kholia/HF-PA-v3/[Final Sim] Screenshot_2021-08-01_14-00-23.png

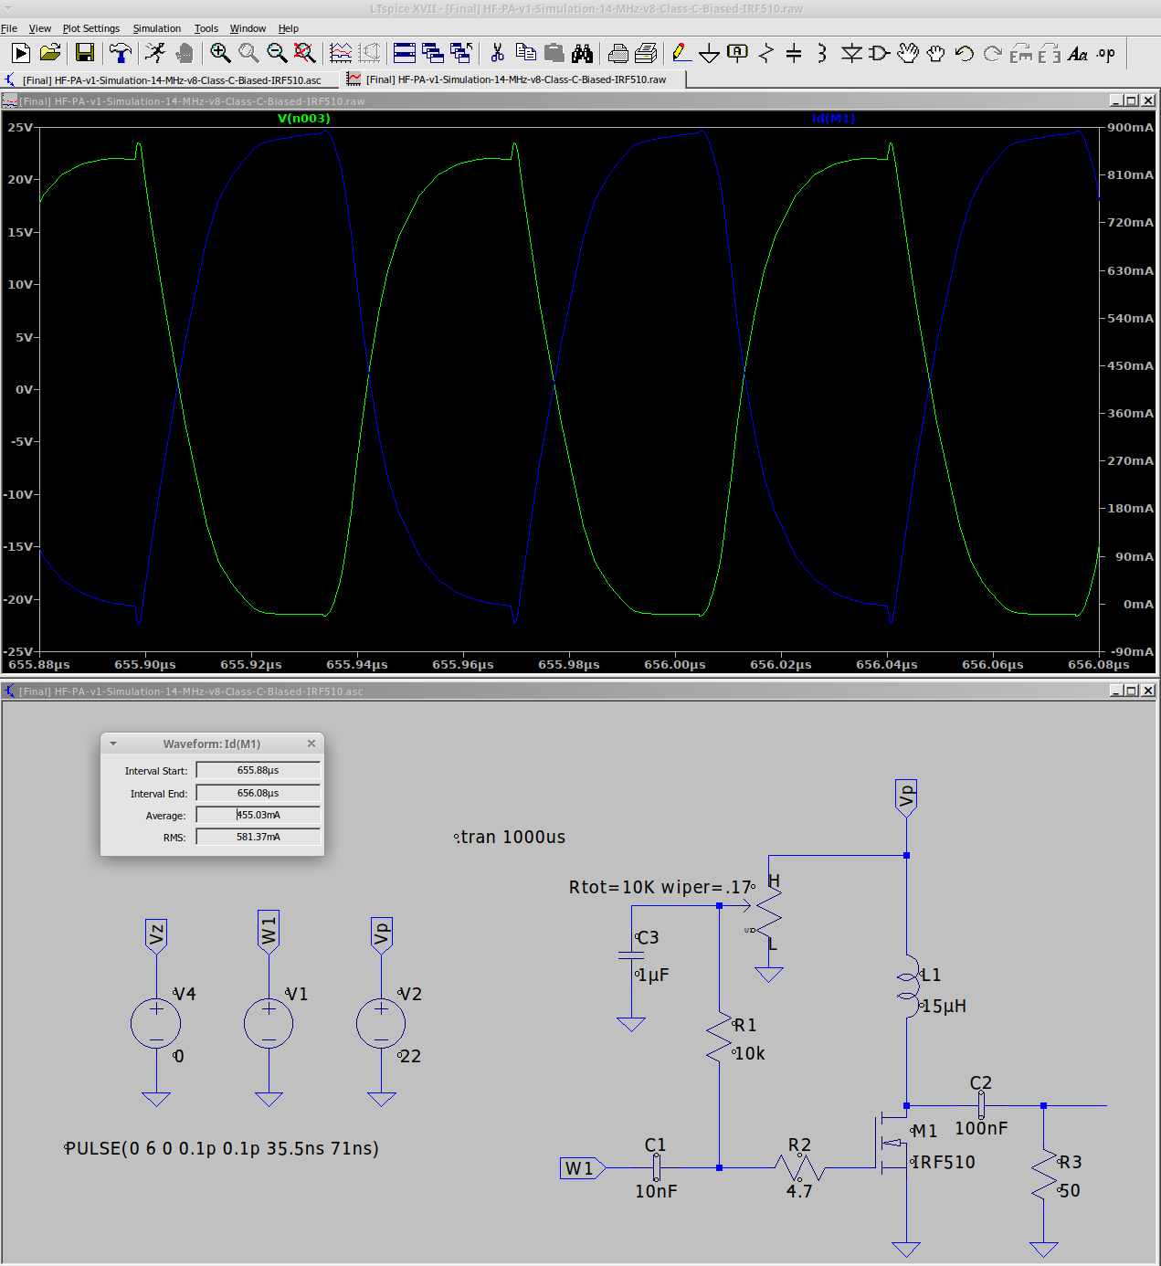
[Final Sim] Screenshot_2021-08-01_14-00-23.png
