kholia/HF-PA-v3/Genuine-Vishay-IRF510/Fun game - Which one is real? [miscdotgeek.com].jpg

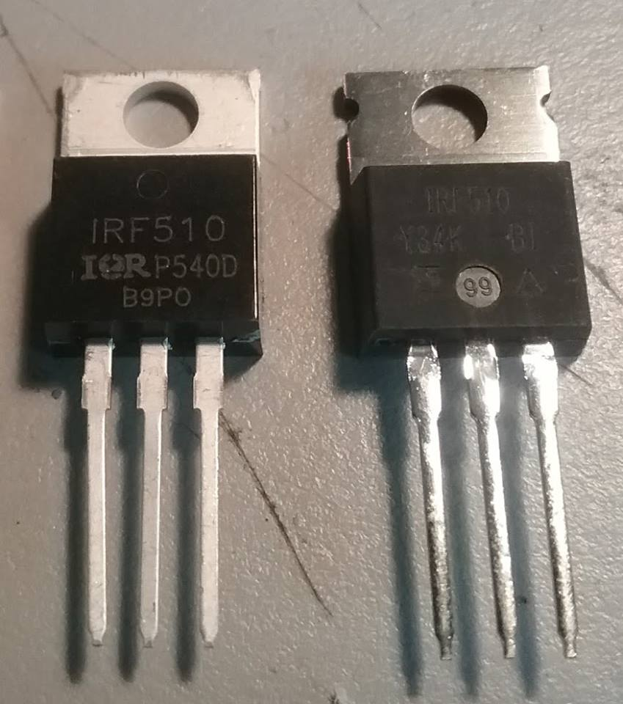
Genuine-Vishay-IRF510/Fun game - Which one is real? [miscdotgeek.com].jpg
