kholia/HF-PA-v3/Genuine-Vishay-IRF510/IRF510 MOSFET N-Channel Power MOSFETs-550x550.jpg

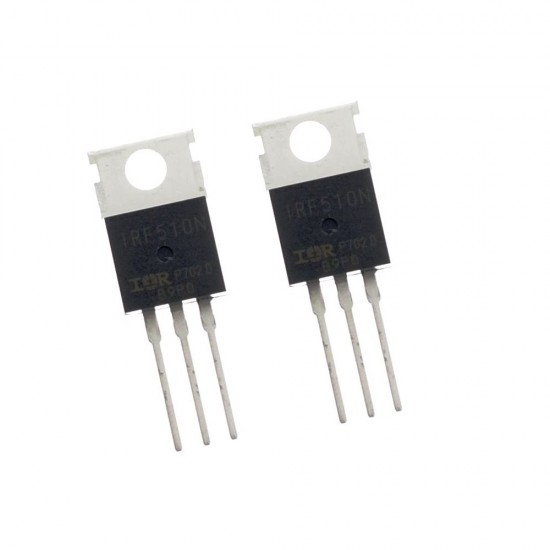
Genuine-Vishay-IRF510/IRF510 MOSFET N-Channel Power MOSFETs-550x550.jpg
