kholia/HF-PA-v3/HF-PA-Simulations/Biasing Not Helping  - Screenshot_2021-07-29_09-07-39.png

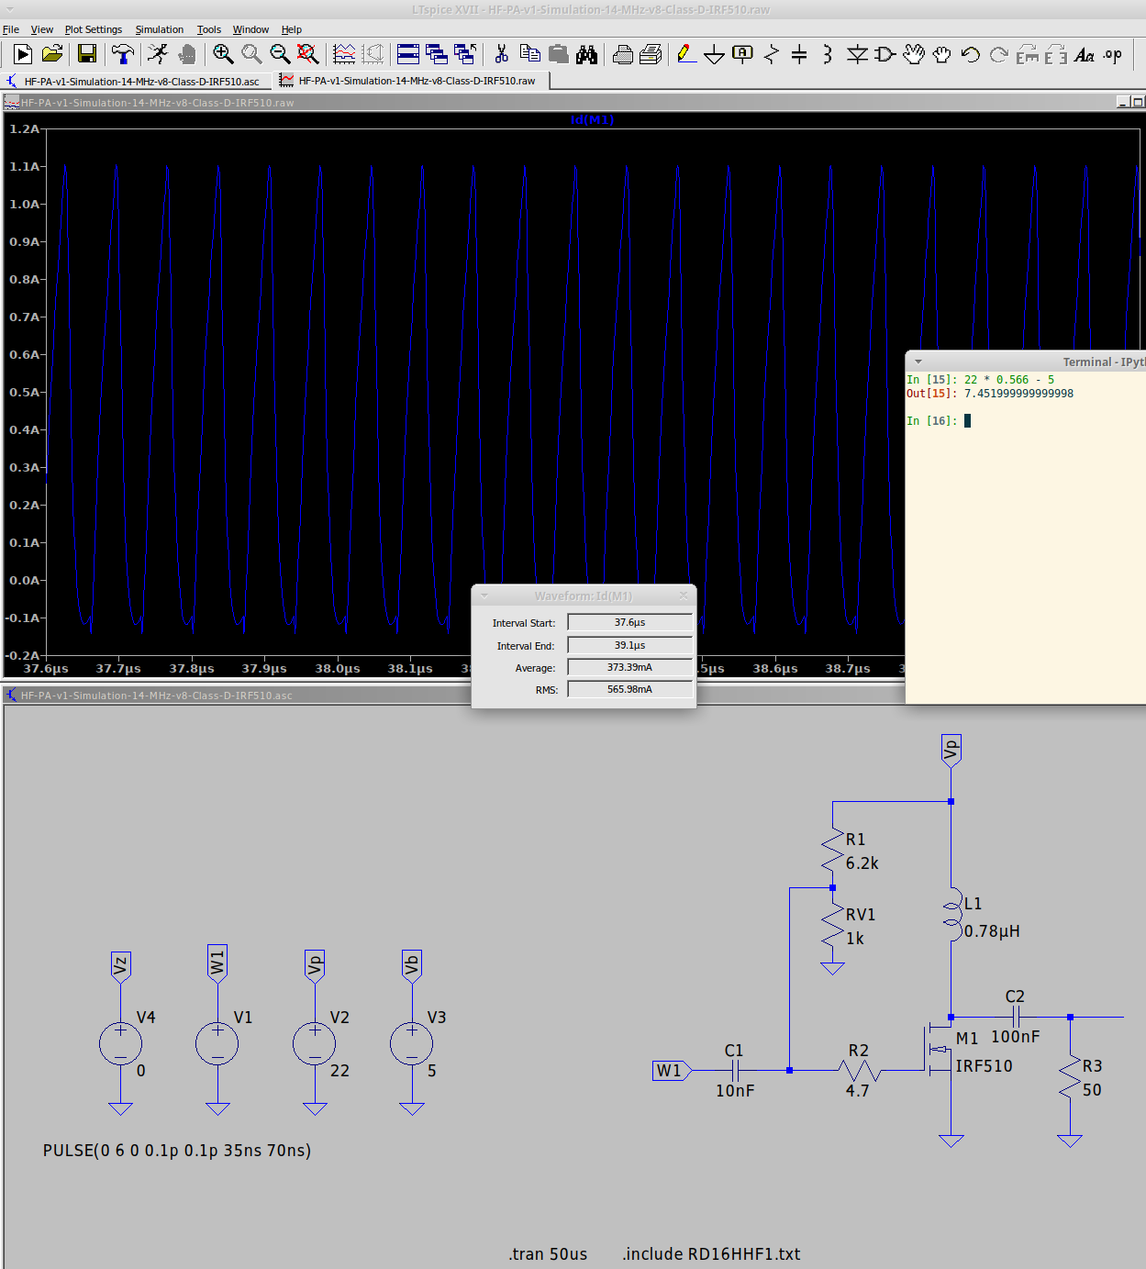
HF-PA-Simulations/Biasing Not Helping - Screenshot_2021-07-29_09-07-39.png
