kholia/HF-PA-v3/HF-PA-Simulations/Higher PA Voltage - Screenshot_2021-07-27_19-01-27.png

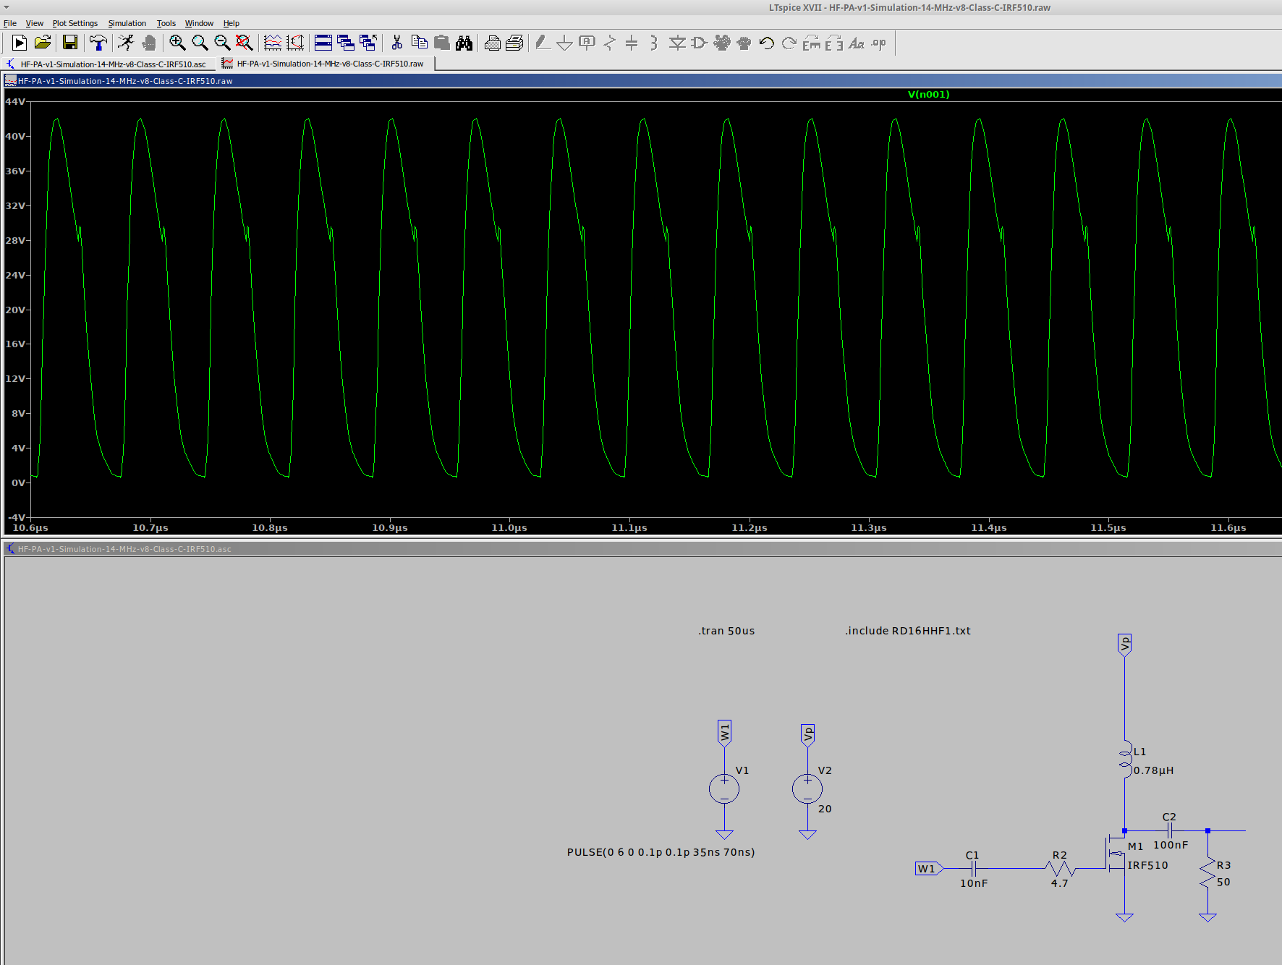
HF-PA-Simulations/Higher PA Voltage - Screenshot_2021-07-27_19-01-27.png
