kholia/HF-PA-v3/HF-PA-Simulations/Screenshot_2021-07-14_15-19-50.png

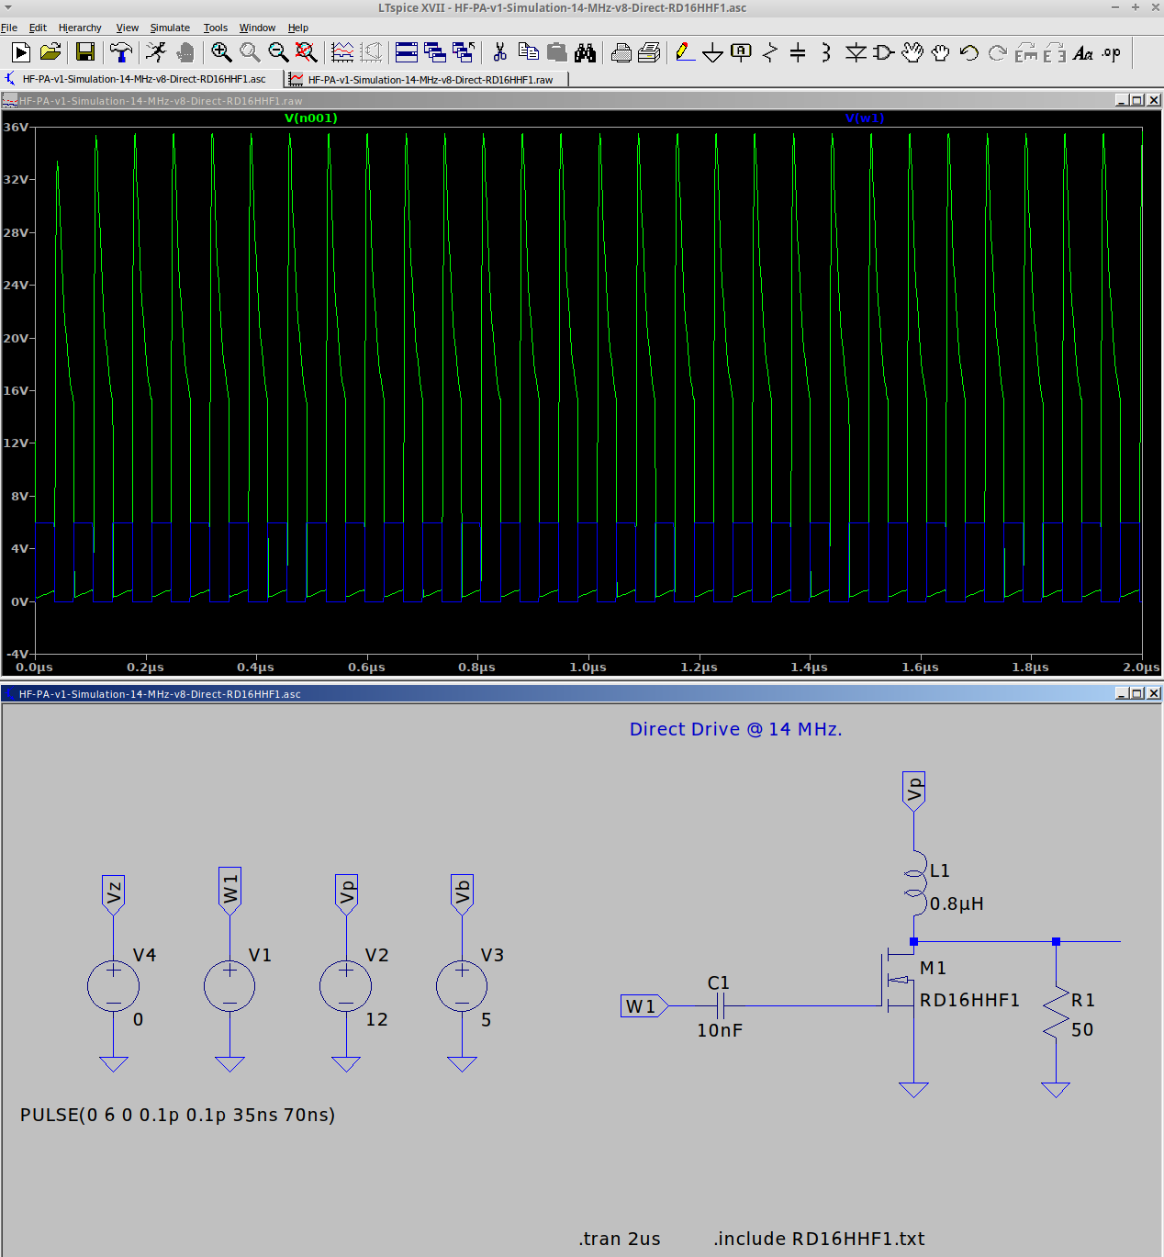
HF-PA-Simulations/Screenshot_2021-07-14_15-19-50.png
