kholia/HF-PA-v3/HF-PA-Simulations/Screenshot_2021-07-14_15-25-21.png

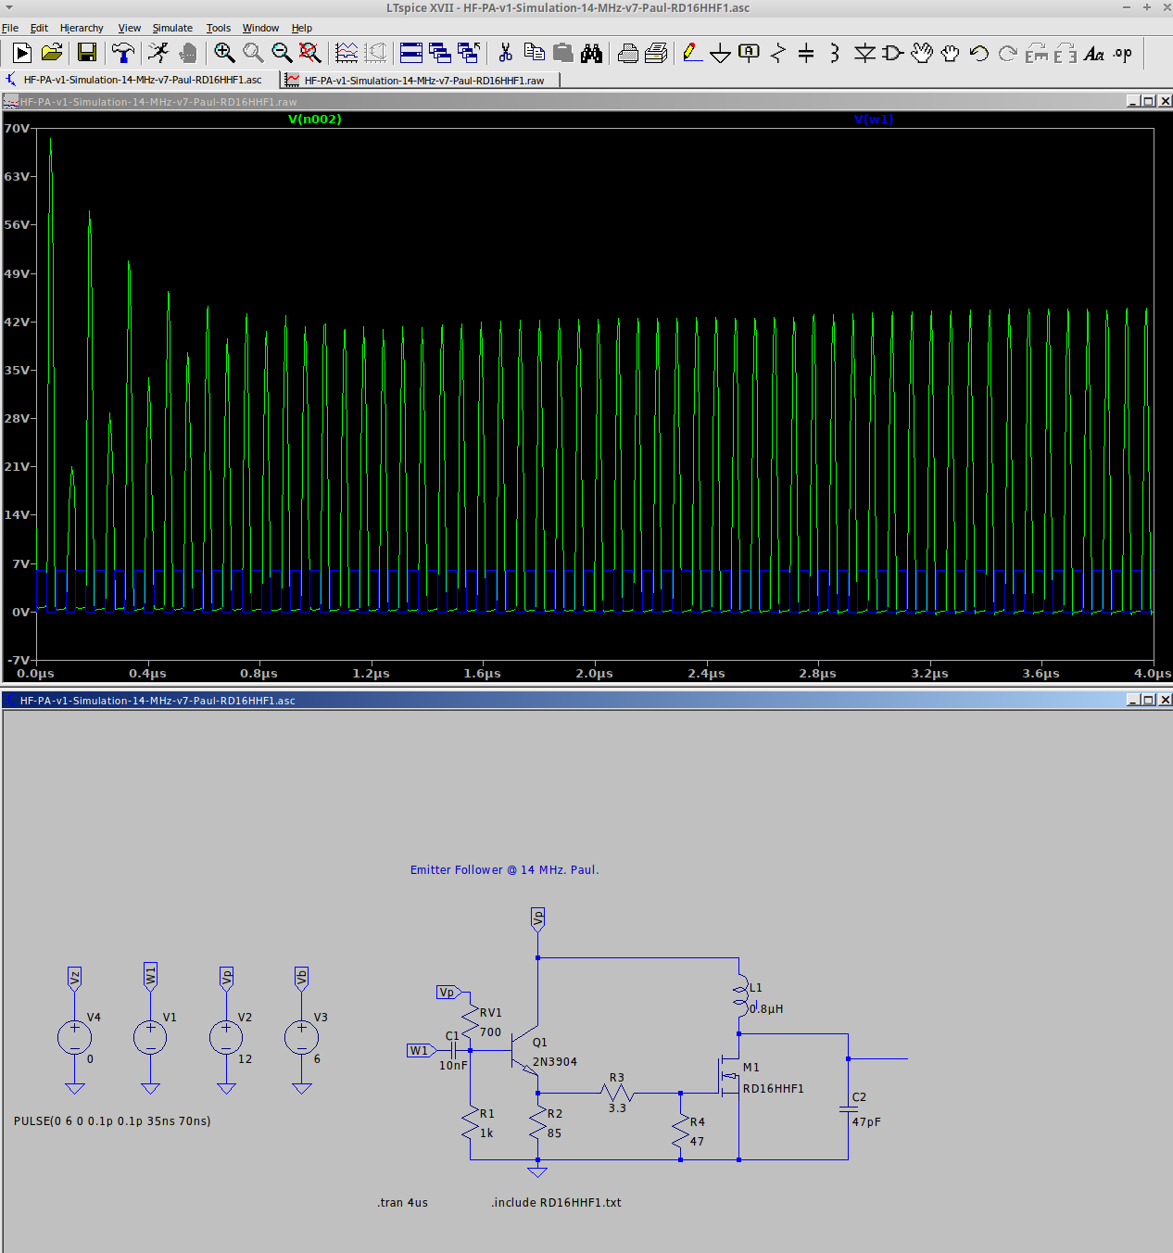
HF-PA-Simulations/Screenshot_2021-07-14_15-25-21.png
