kholia/HF-PA-v3/HF-PA-Simulations/Screenshot_2021-07-22_14-25-35.png

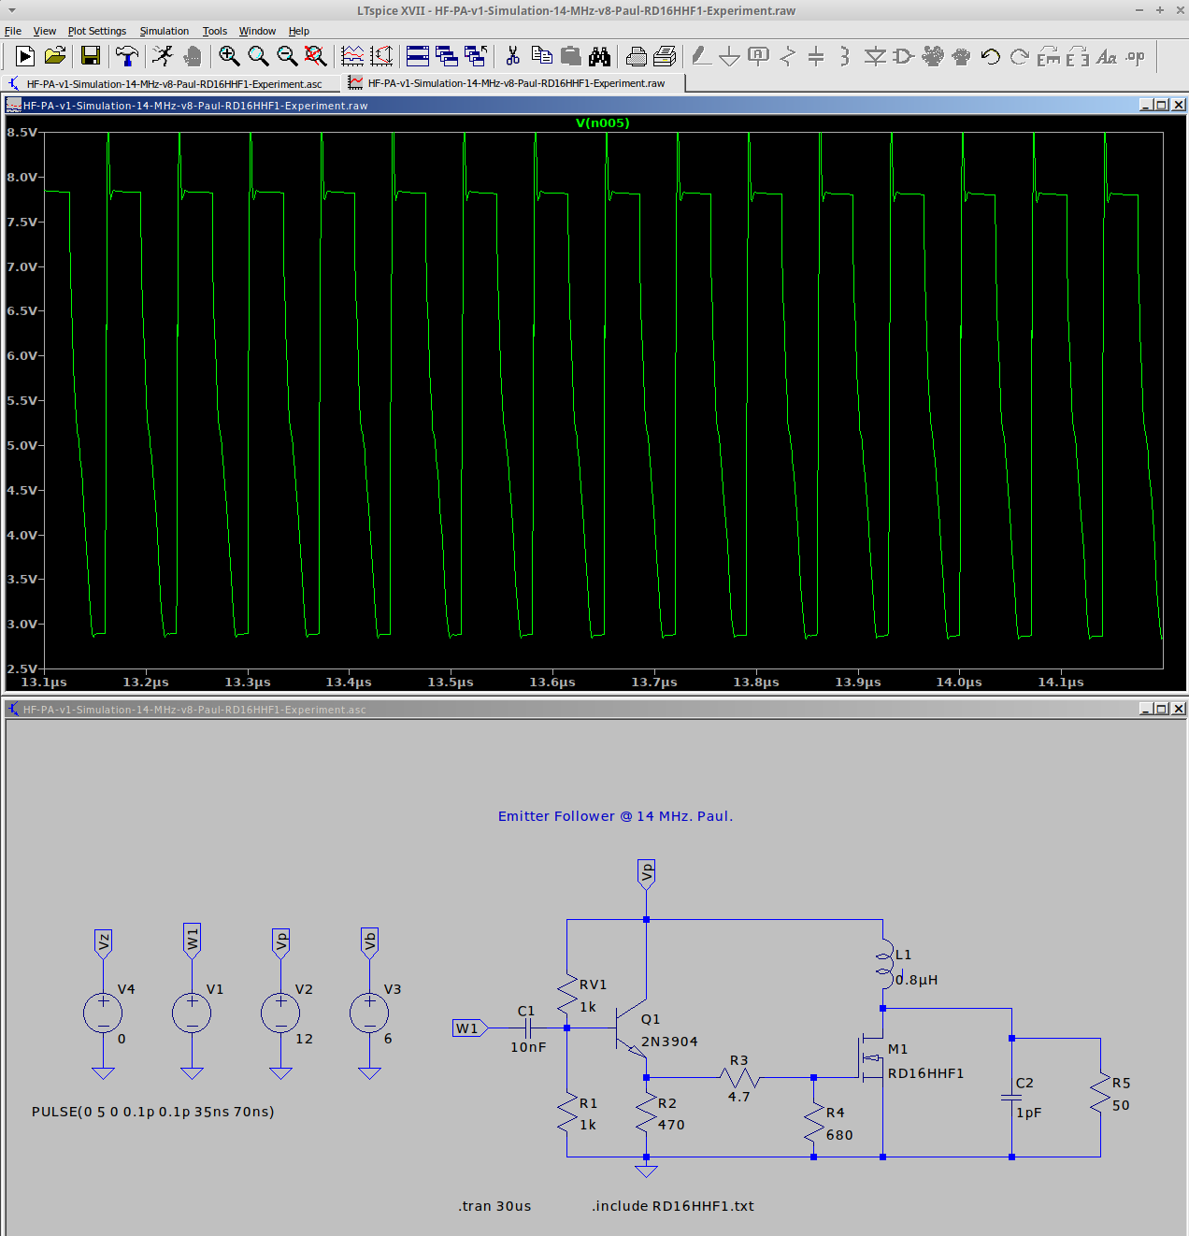
HF-PA-Simulations/Screenshot_2021-07-22_14-25-35.png
