kholia/HF-PA-v3/HF-PA-Simulations/Screenshot_2021-07-22_22-05-22.png

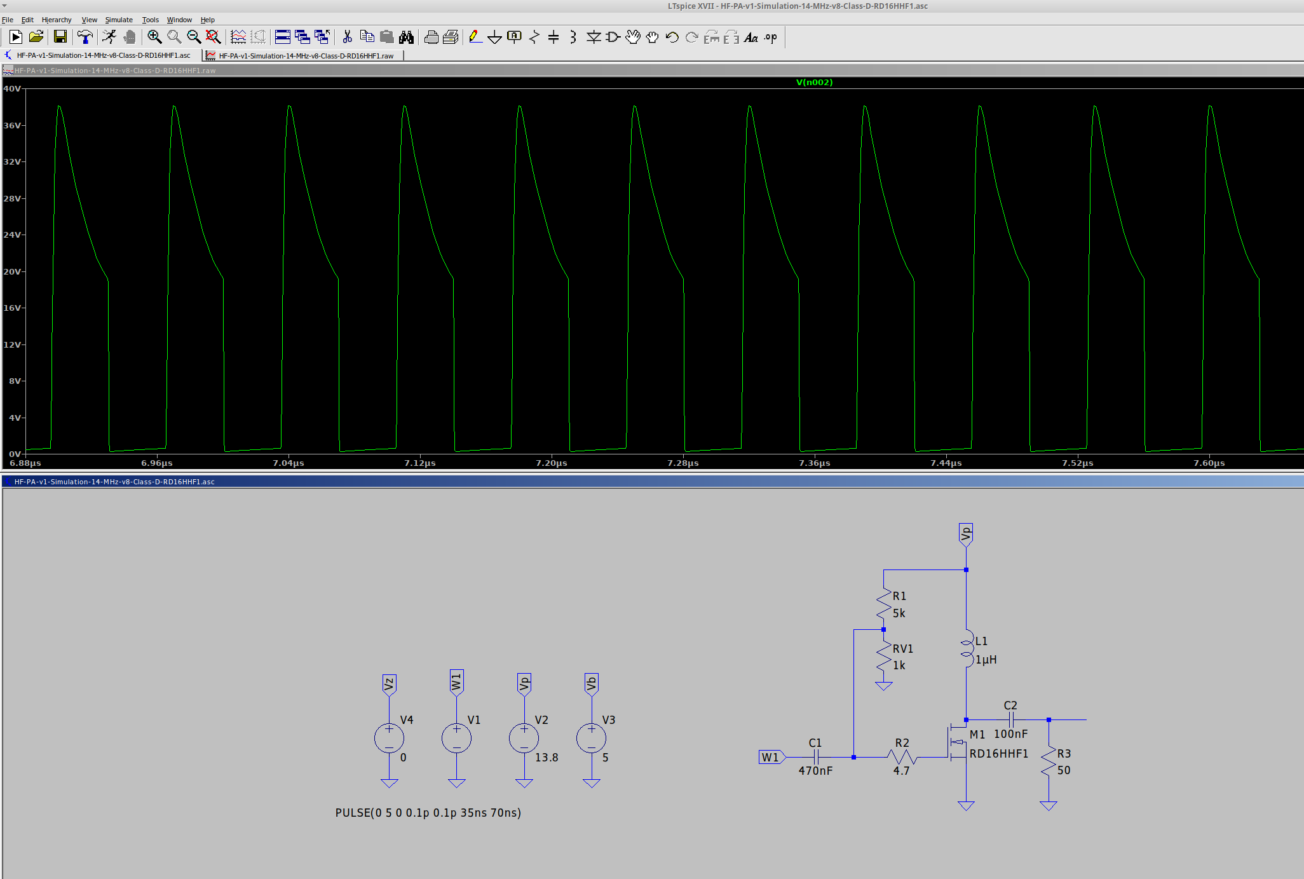
HF-PA-Simulations/Screenshot_2021-07-22_22-05-22.png
