kholia/HF-PA-v3/HF-PA-Simulations/Screenshot_2021-07-27_22-03-09.png

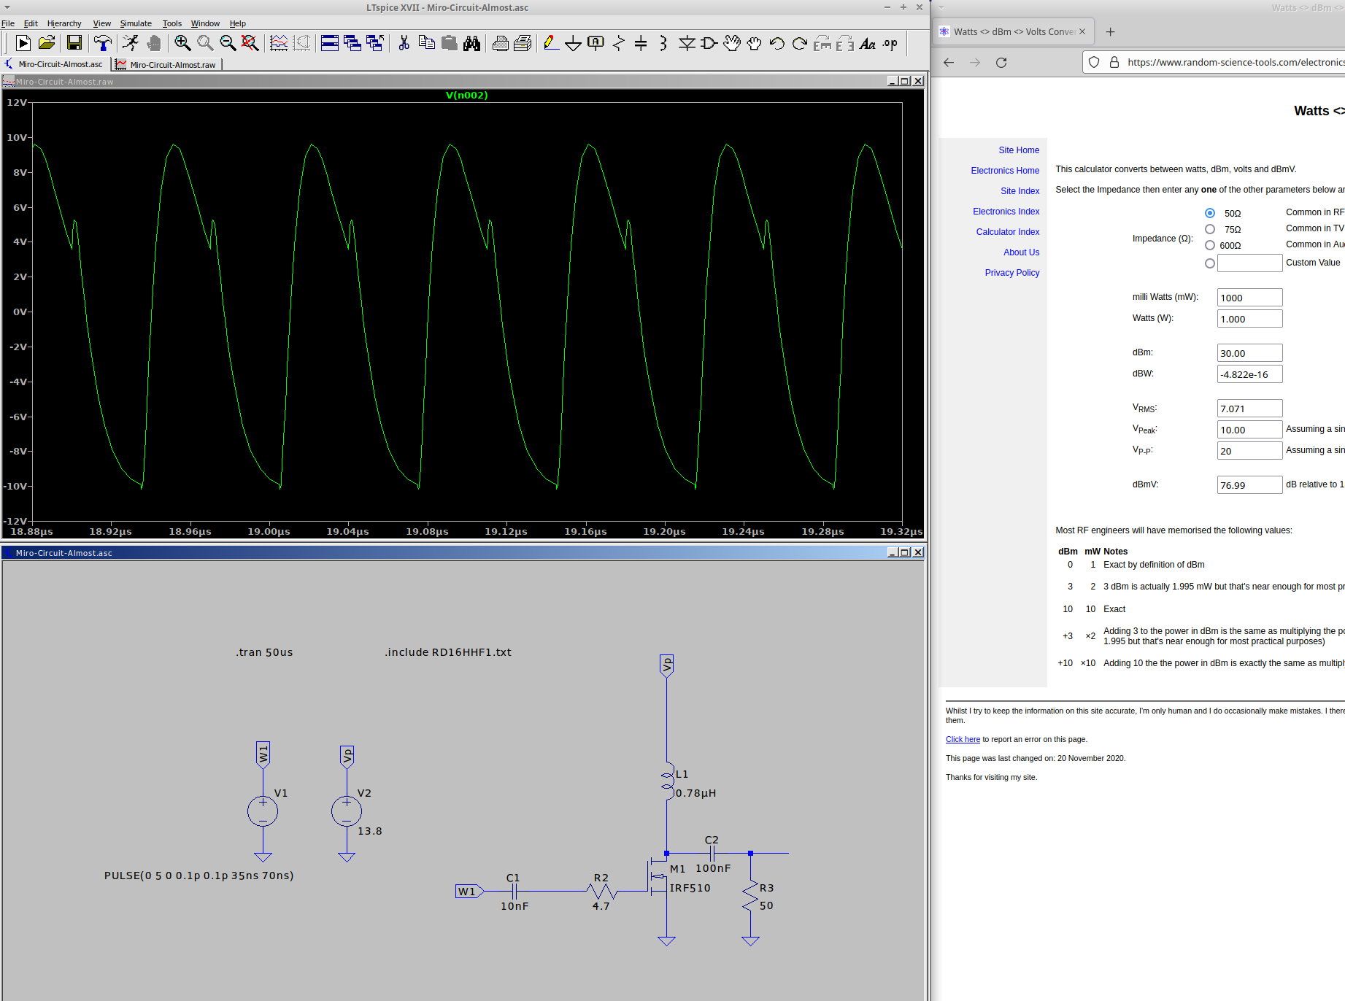
HF-PA-Simulations/Screenshot_2021-07-27_22-03-09.png
