kholia/HF-PA-v3/HF-PA-Simulations/Screenshot_2021-07-27_22-06-03.png

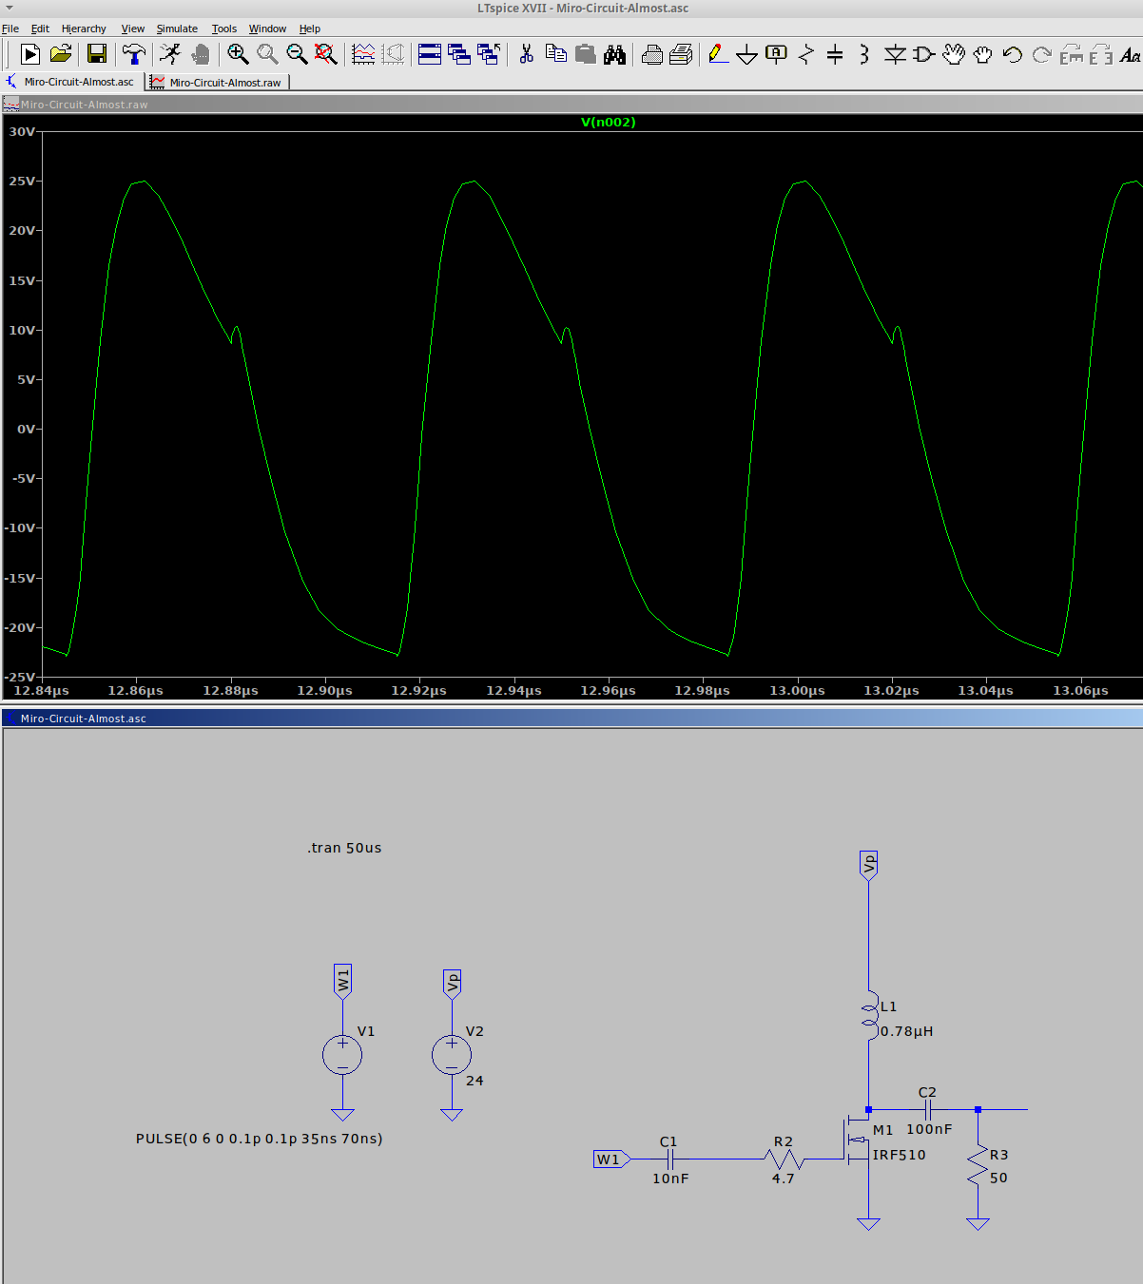
HF-PA-Simulations/Screenshot_2021-07-27_22-06-03.png
