kholia/HF-PA-v3/HF-PA-Simulations/Screenshot_2021-07-28_18-34-36.png

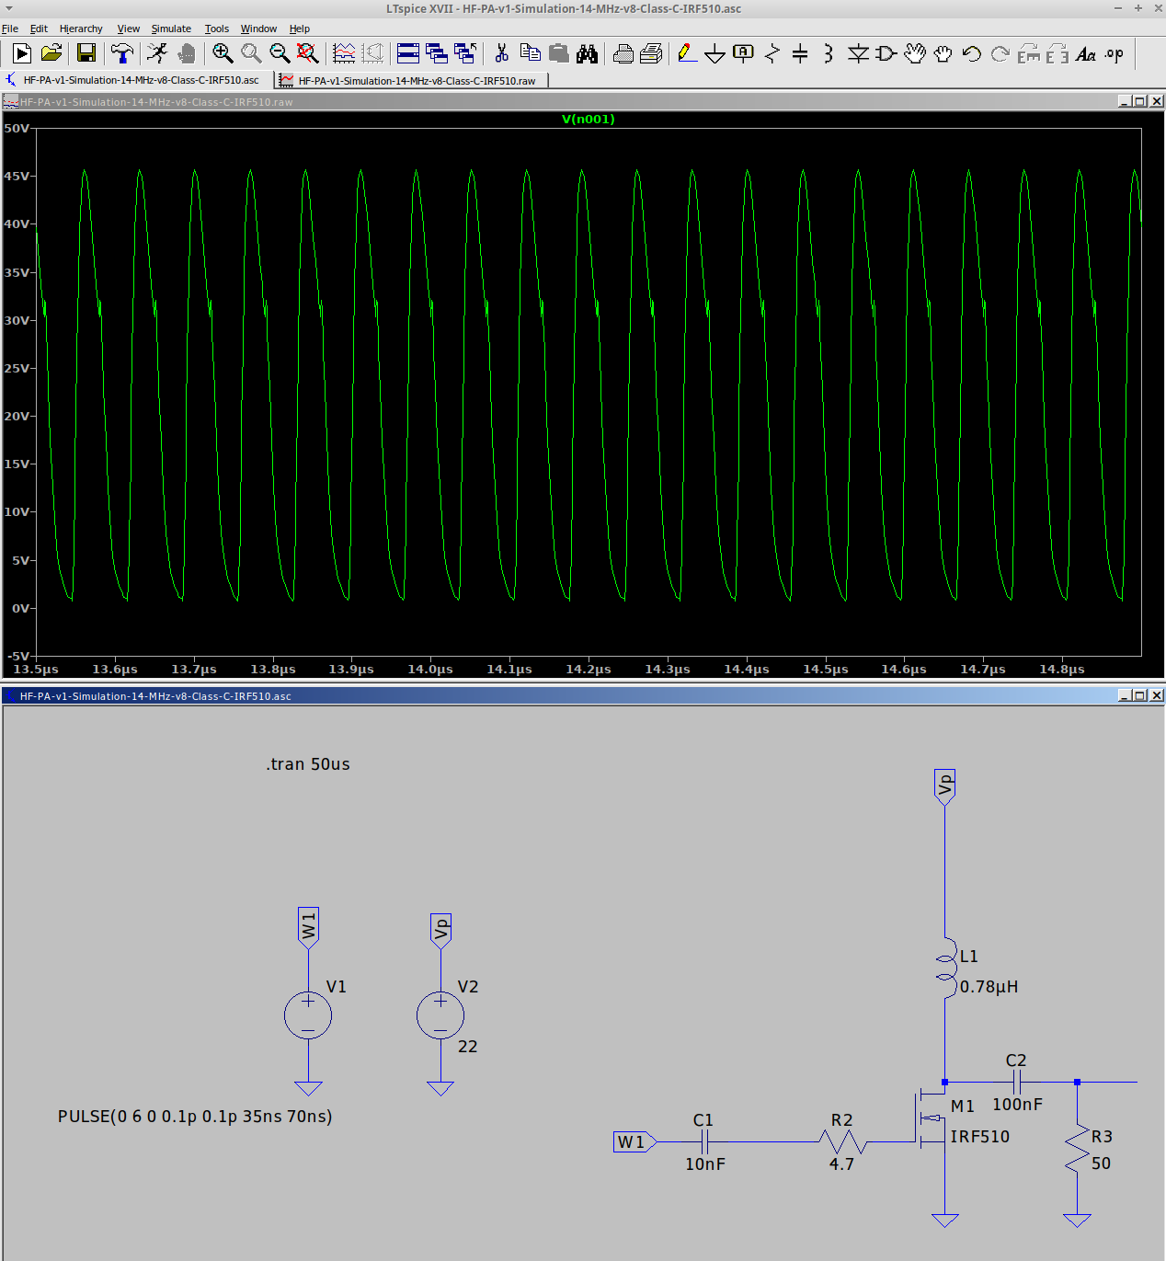
HF-PA-Simulations/Screenshot_2021-07-28_18-34-36.png
