kholia/HF-PA-v3/HF-PA-Simulations/Screenshot_2021-07-29_00-05-49.png

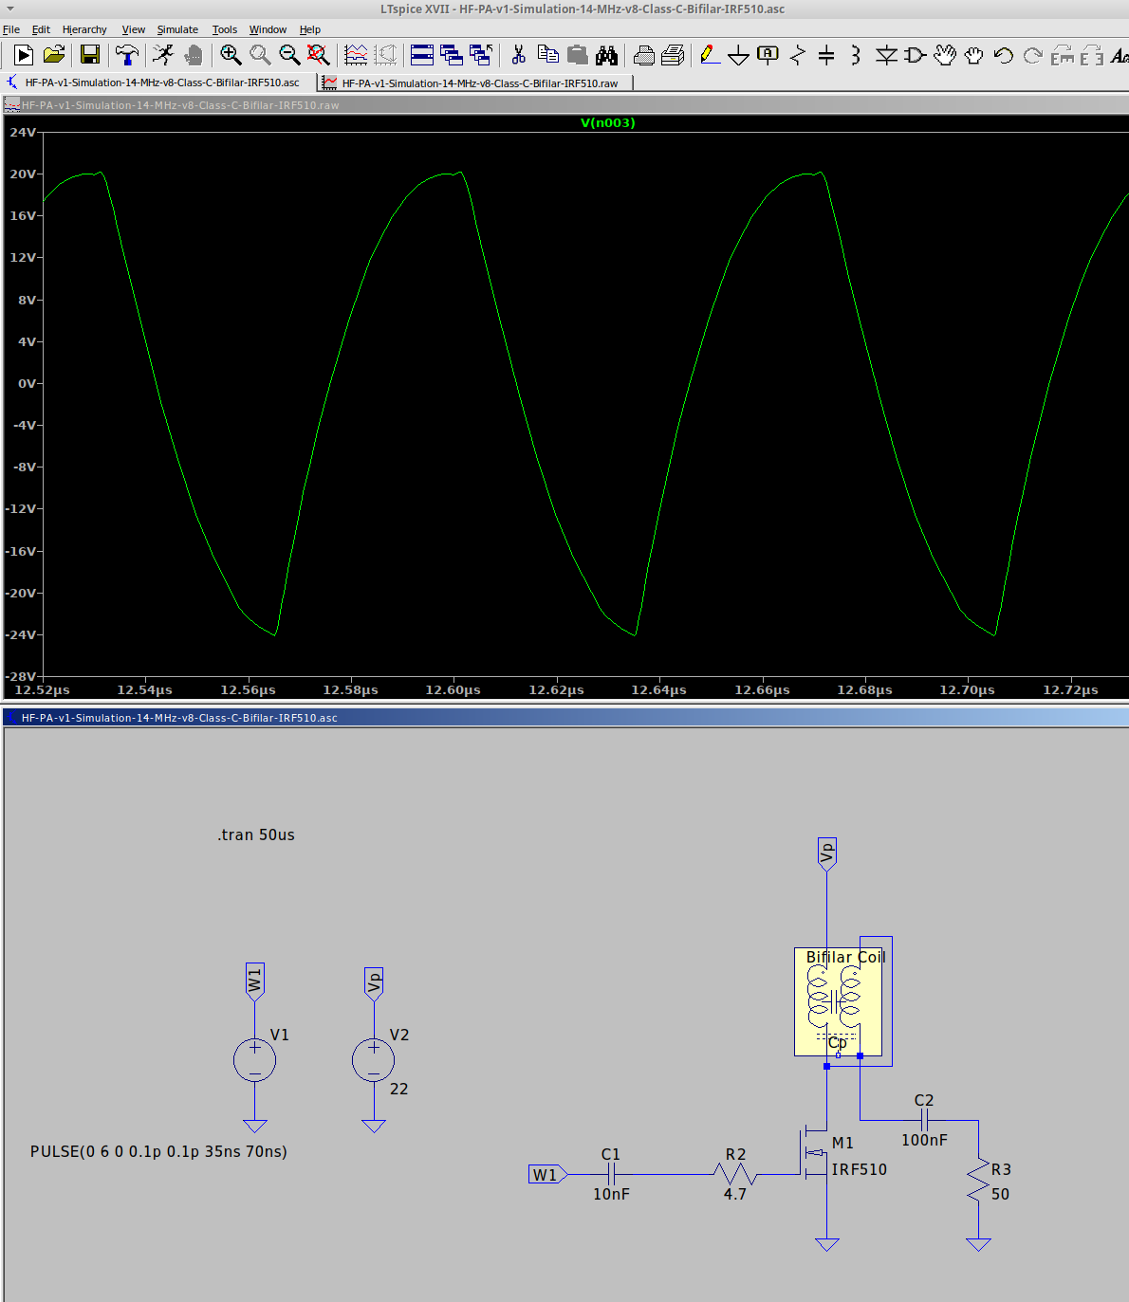
HF-PA-Simulations/Screenshot_2021-07-29_00-05-49.png
