kholia/HF-PA-v3/HF-PA-Simulations/Screenshot_2021-07-29_00-10-33.png

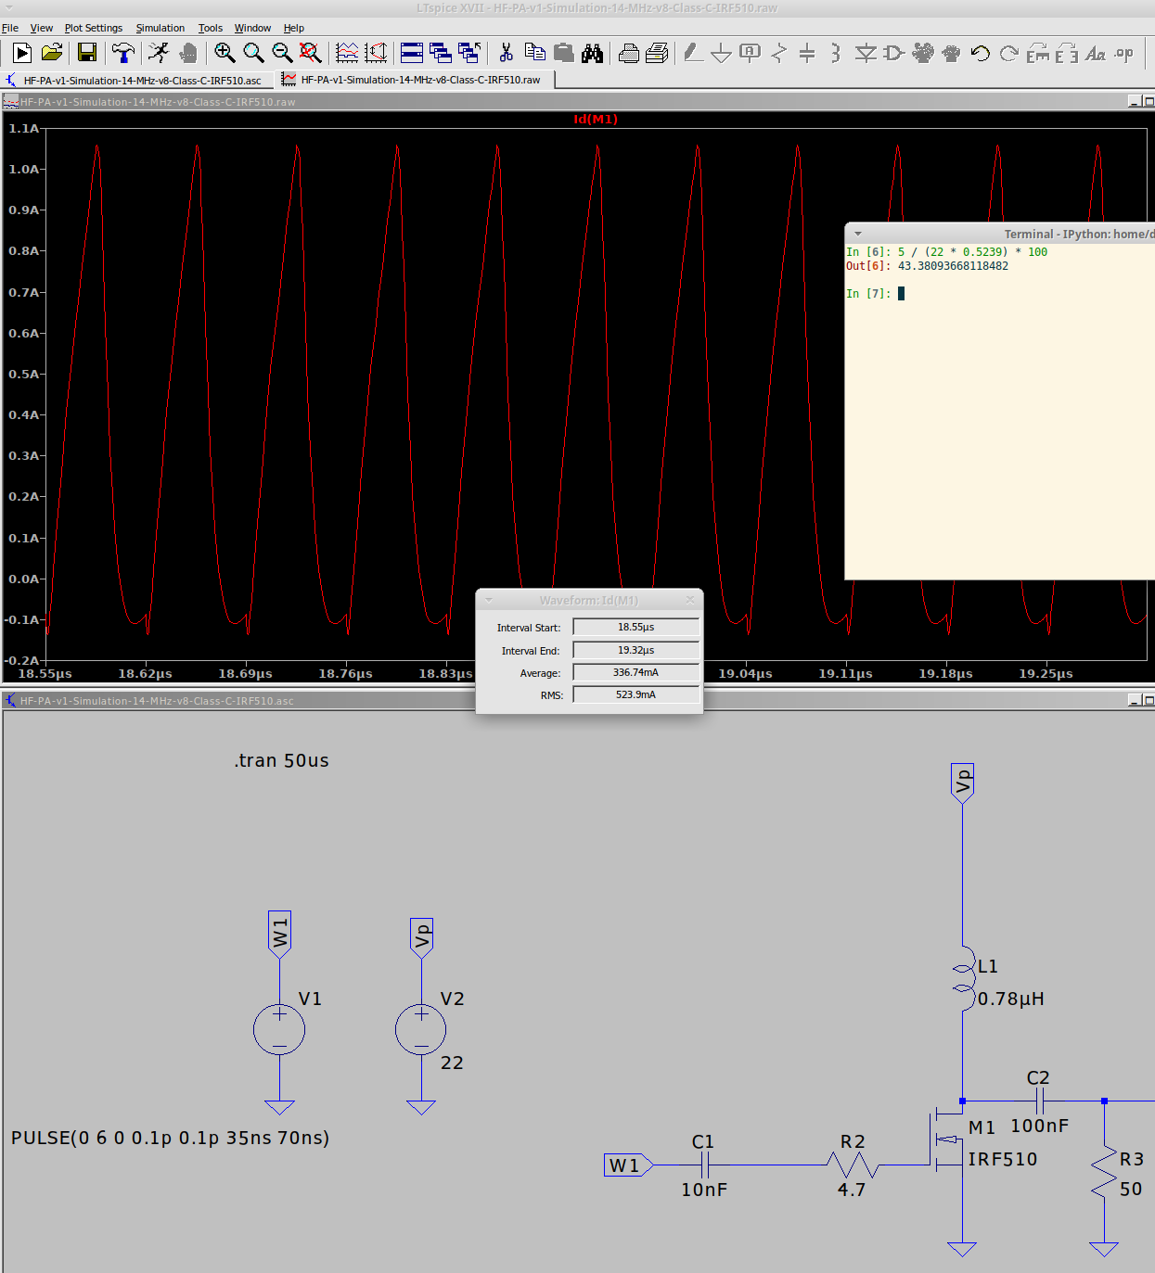
HF-PA-Simulations/Screenshot_2021-07-29_00-10-33.png
