kholia/HF-PA-v3/Info/40m-lpf-filter-as-built.png

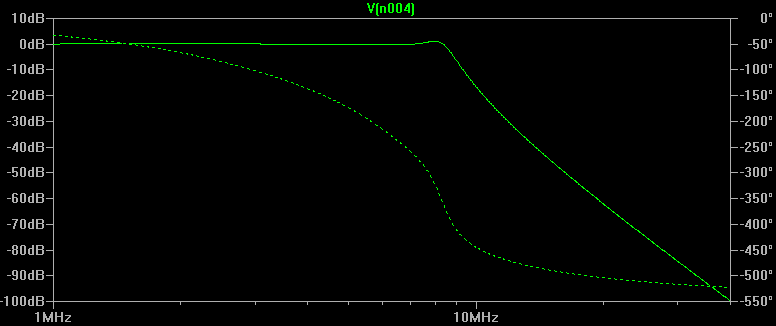
Info/40m-lpf-filter-as-built.png
