kholia/HF-PA-v3/Info/1513-2-550x550w.JPG

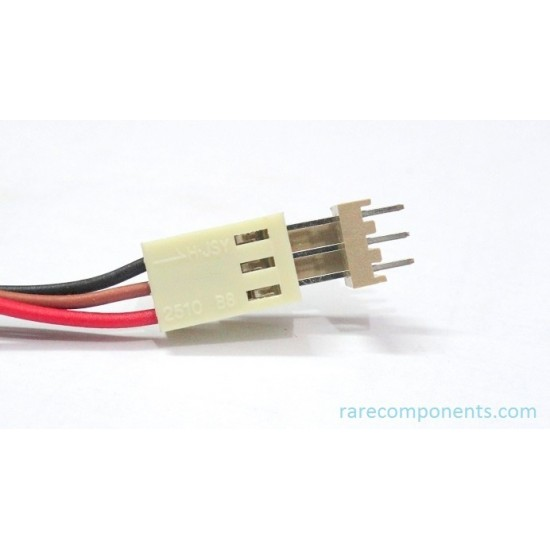
Info/1513-2-550x550w.JPG
