kholia/HF-PA-v3/Info/[Earthing Tip] - Screenshot_2021-07-30_19-18-58.png

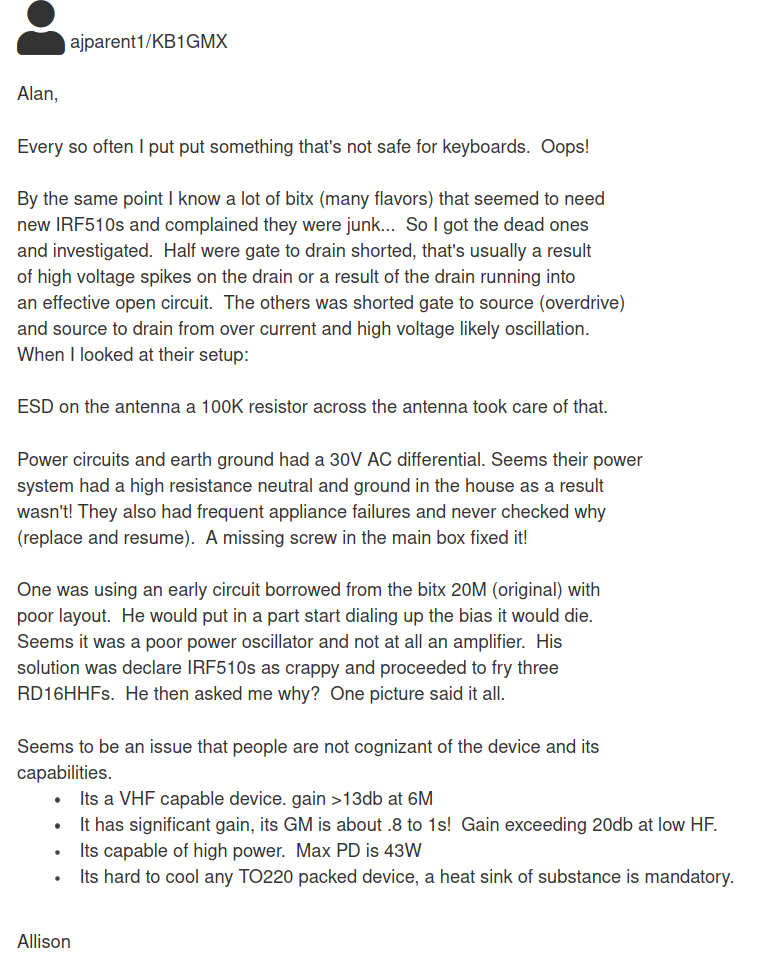
Info/[Earthing Tip] - Screenshot_2021-07-30_19-18-58.png
