kholia/HF-PA-v3/Info/fan-circuit-pulldown-640x349.png

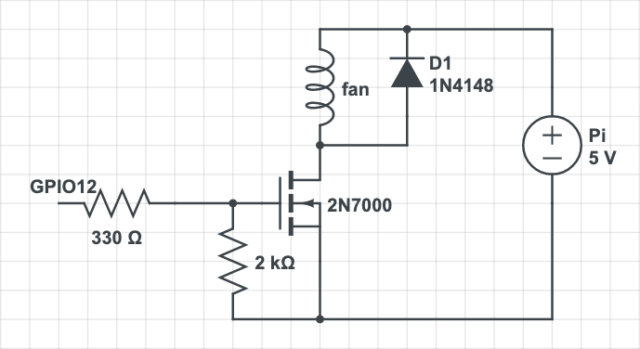
Info/fan-circuit-pulldown-640x349.png
