kholia/HF-PA-v3/Info/IRF510-mod.jpeg

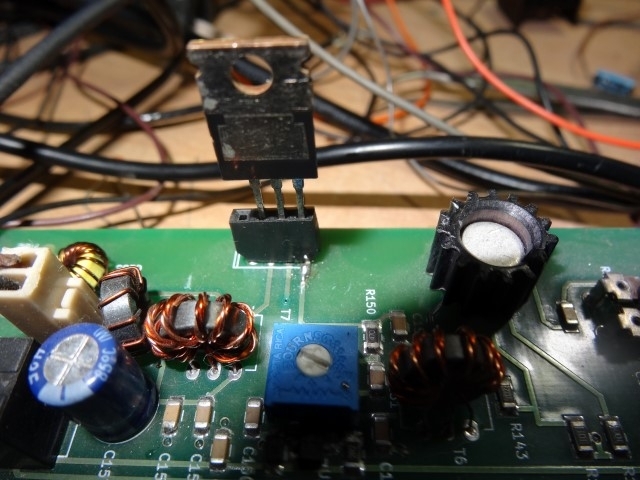
Info/IRF510-mod.jpeg
