kholia/HF-PA-v3/Info/kk9jef-lpf.jpg

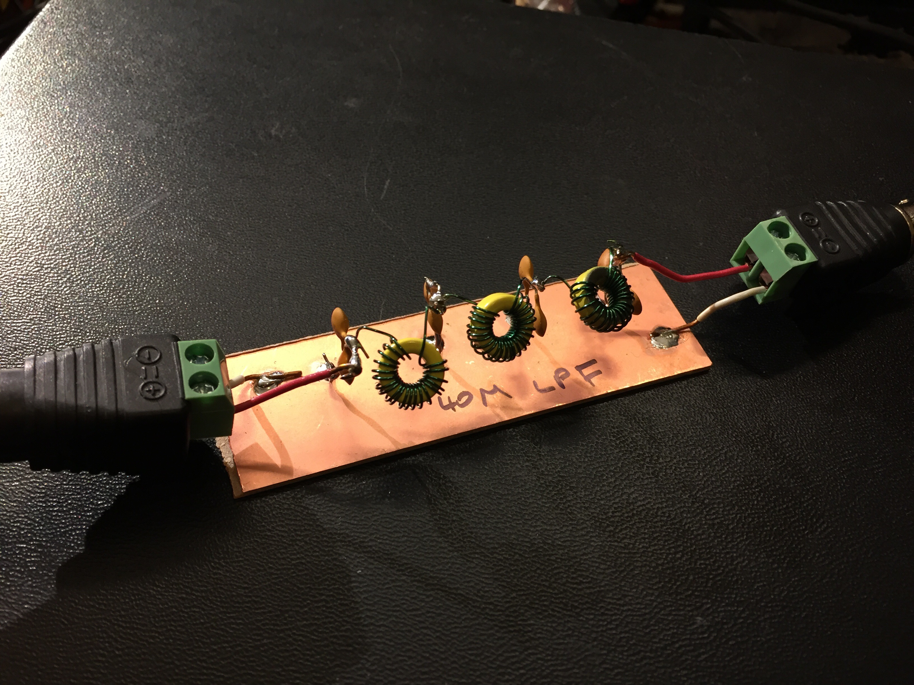
Info/kk9jef-lpf.jpg
