kholia/HF-PA-v3/Info/LPF-Details-Screenshot_2021-09-19_14-00-25.png

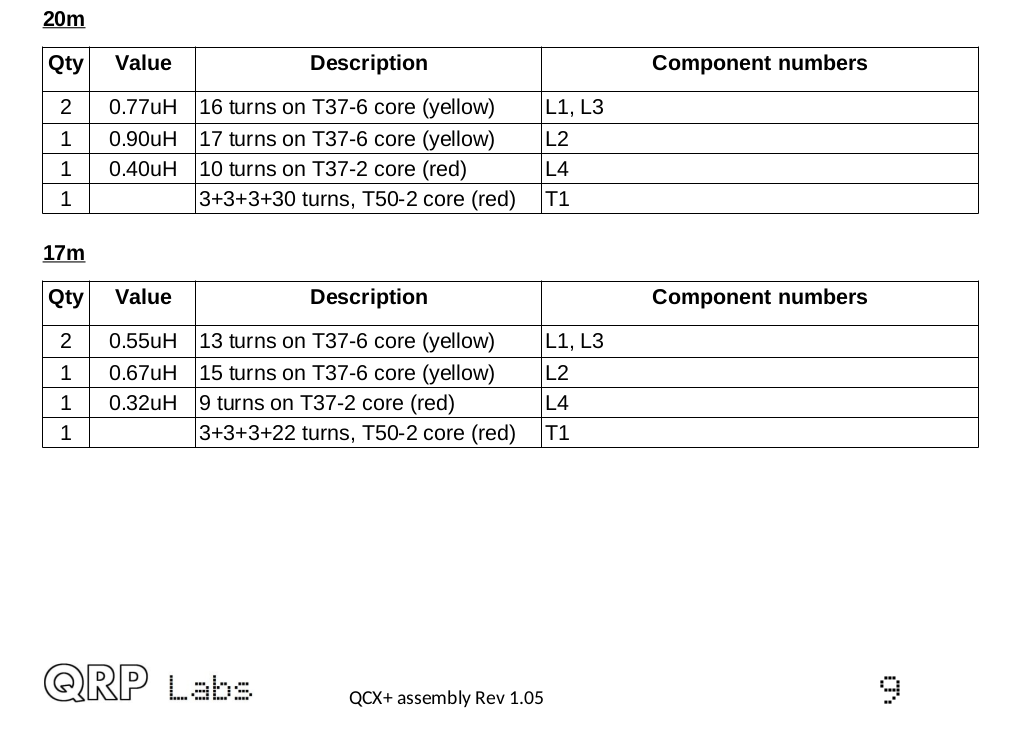
Info/LPF-Details-Screenshot_2021-09-19_14-00-25.png
