kholia/HF-PA-v3/Info/LPF-Screenshot_2021-09-19_14-16-24.png

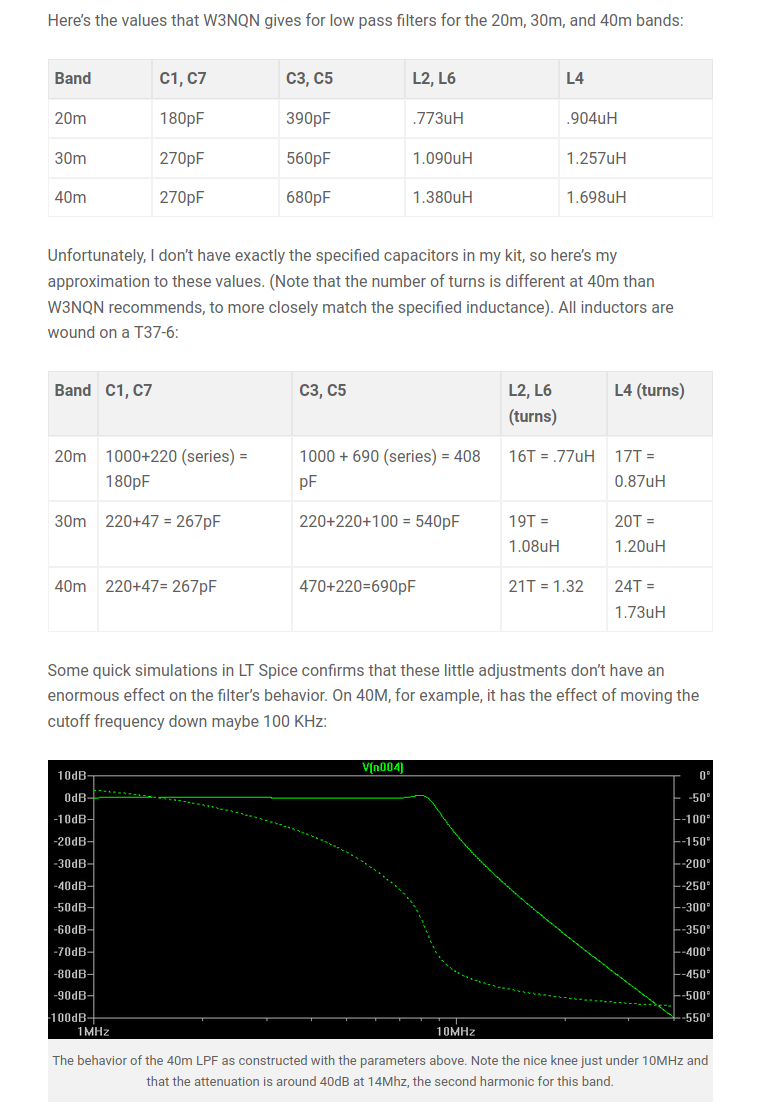
Info/LPF-Screenshot_2021-09-19_14-16-24.png
