kholia/HF-PA-v3/Info/lpf-sketch.png

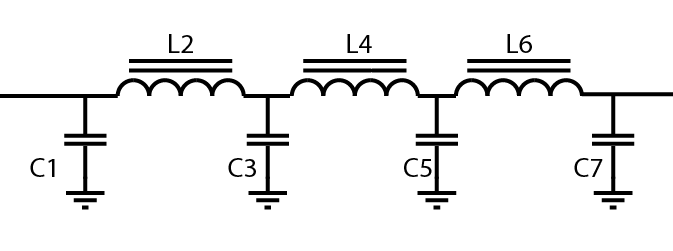
Info/lpf-sketch.png
