kholia/HF-PA-v3/Info/lulu-RF.bmp

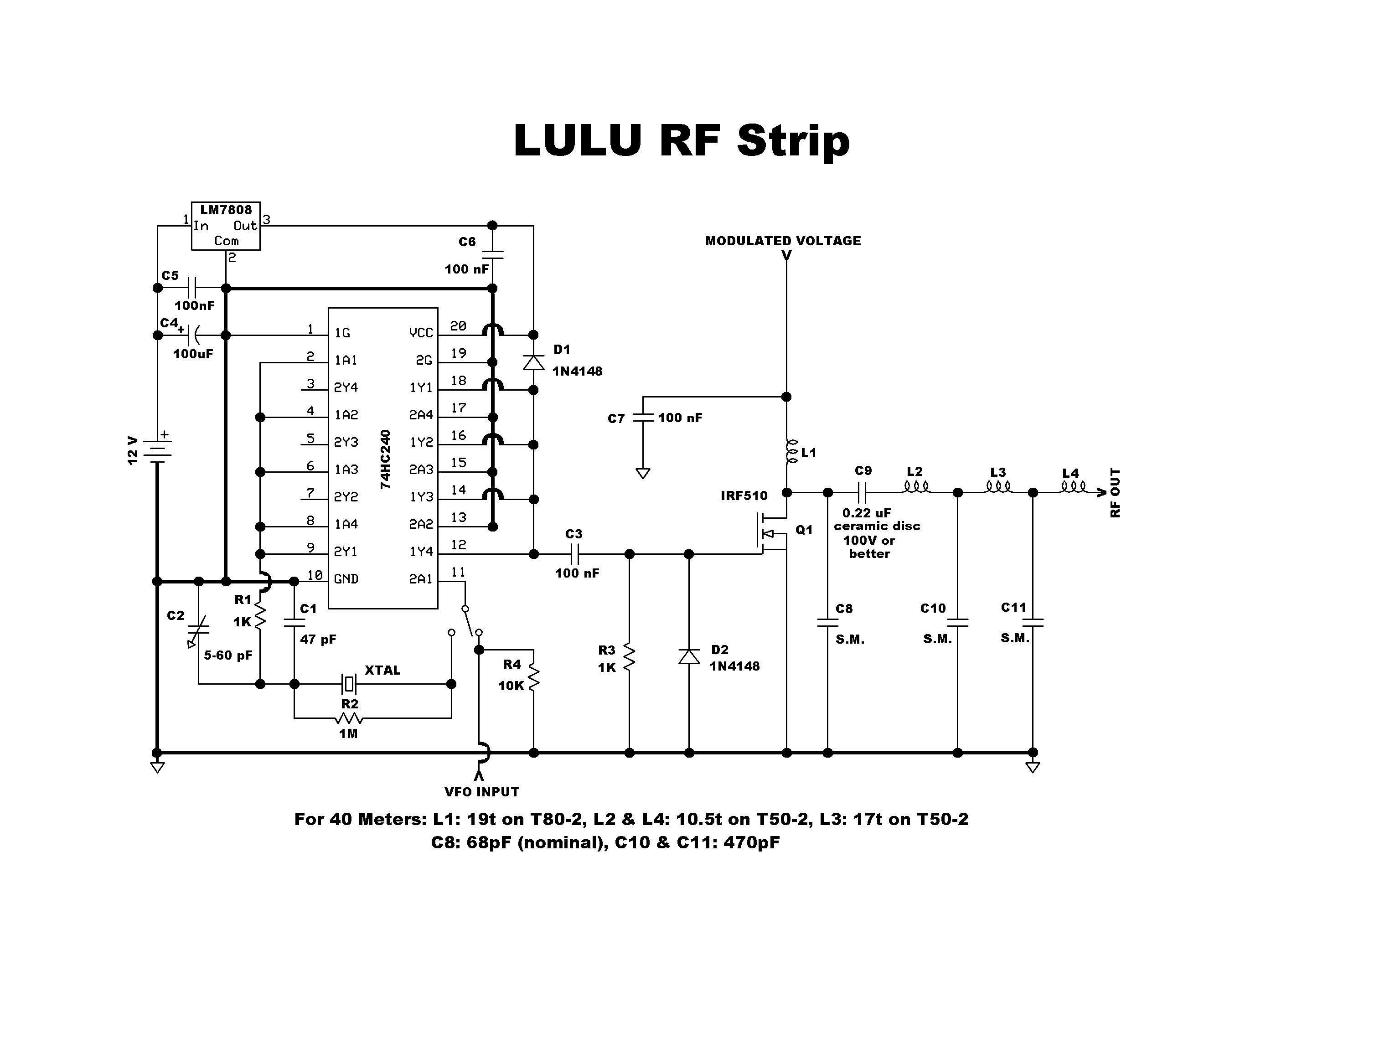
Info/lulu-RF.bmp
