kholia/HF-PA-v3/Info/Mini3.jpg

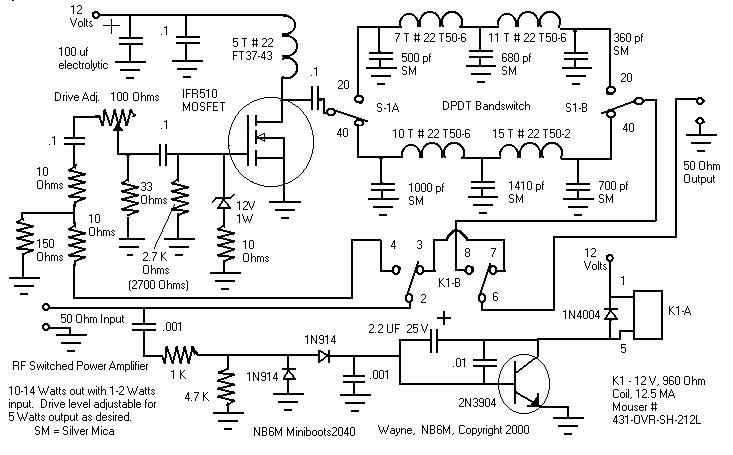
Info/Mini3.jpg
