kholia/HF-PA-v3/Info/Mini4.jpg

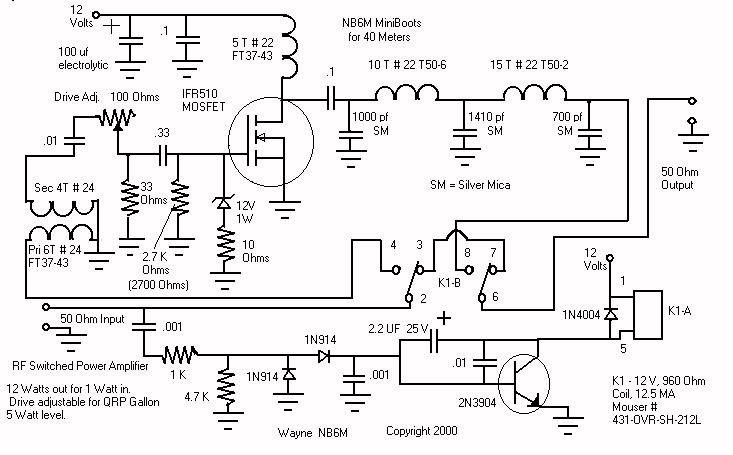
Info/Mini4.jpg
