kholia/HF-PA-v3/Info/mt3608-2a-power-booster-module-800x800.jpg

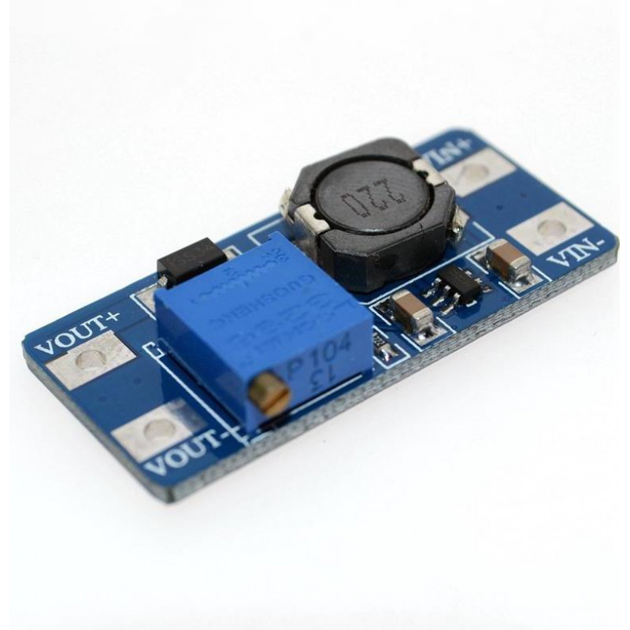
Info/mt3608-2a-power-booster-module-800x800.jpg
