kholia/HF-PA-v3/Info/pa.jpg

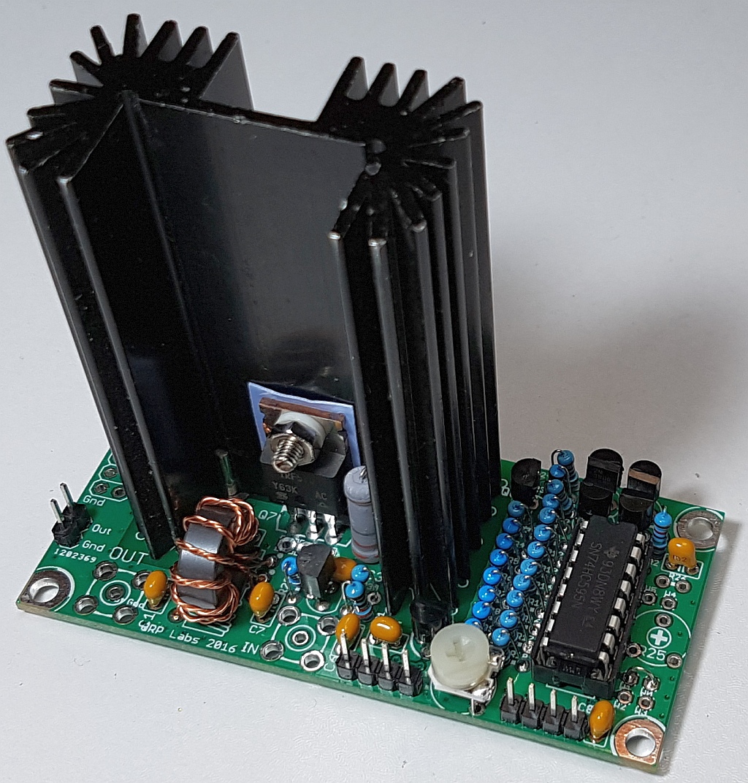
Info/pa.jpg
