kholia/HF-PA-v3/Info/PA_schema.jpg

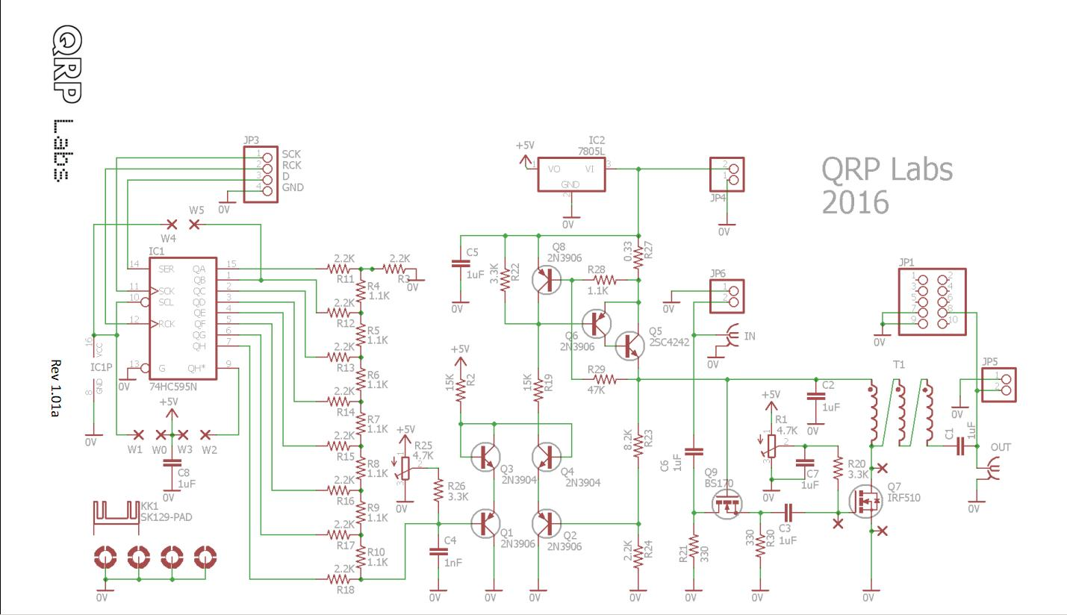
Info/PA_schema.jpg
