kholia/HF-PA-v3/Info/potentiometer_circuit.jpg

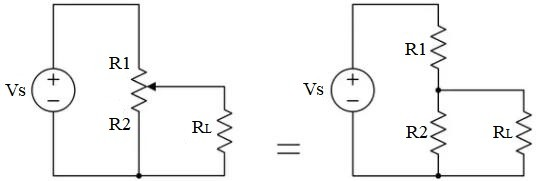
Info/potentiometer_circuit.jpg
