kholia/HF-PA-v3/Info/QCX-HiRes.png

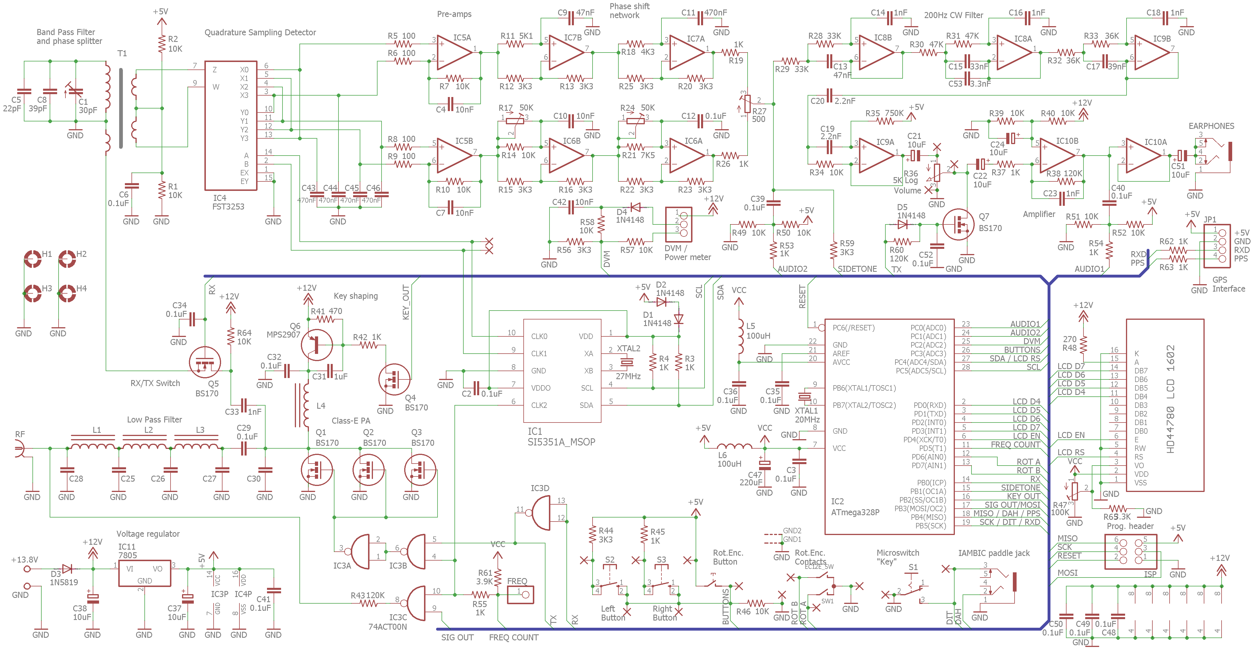
Info/QCX-HiRes.png
