kholia/HF-PA-v3/Info/QCX-LPF-Screenshot_2021-07-29_09-45-46.png

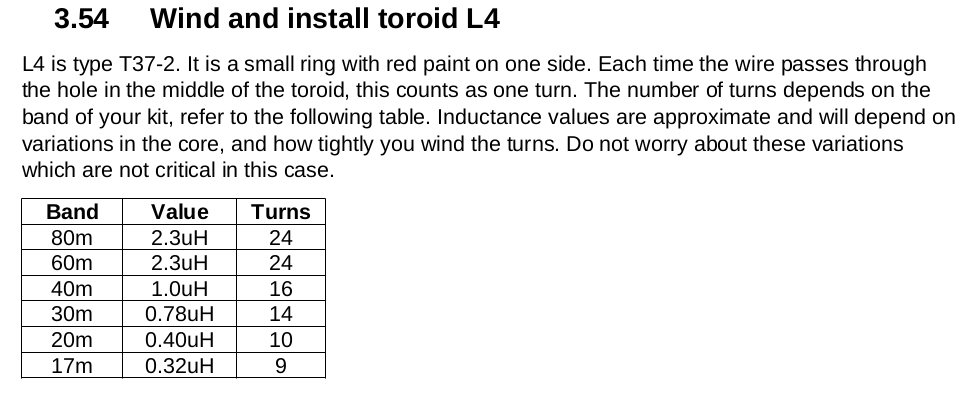
Info/QCX-LPF-Screenshot_2021-07-29_09-45-46.png
