kholia/HF-PA-v3/Info/Screenshot_2021-07-30_20-11-25.png

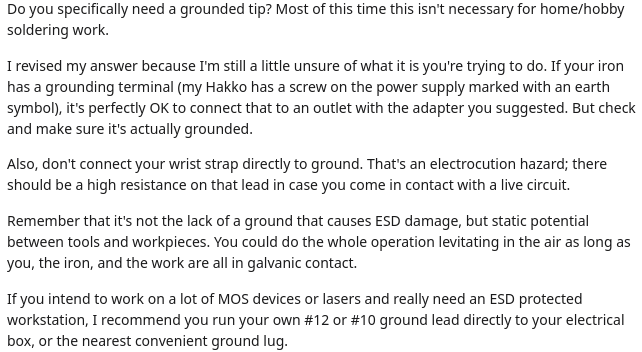
Info/Screenshot_2021-07-30_20-11-25.png
