kholia/HF-PA-v3/Info/Screenshot_2021-08-02_11-49-40.png

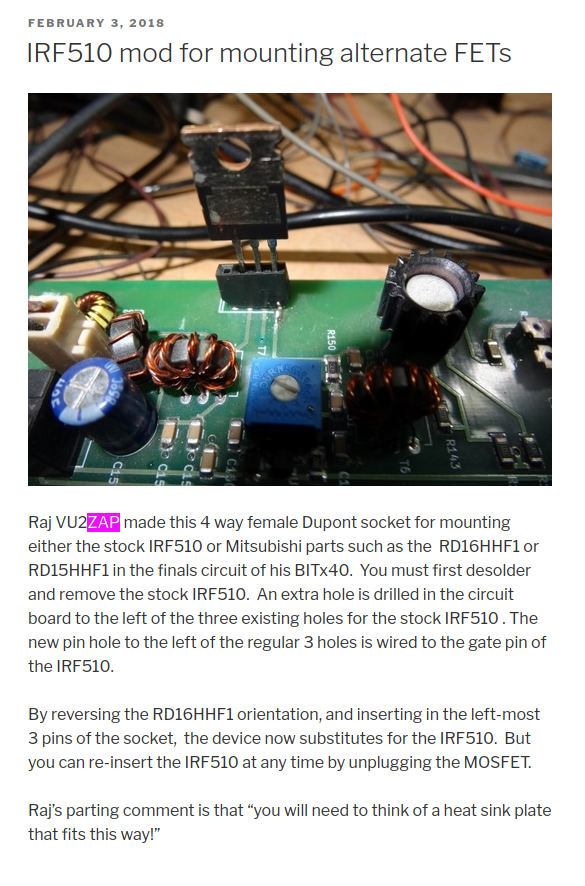
Info/Screenshot_2021-08-02_11-49-40.png
