kholia/HF-PA-v3/Info/Screenshot_2021-09-03_19-26-44.png

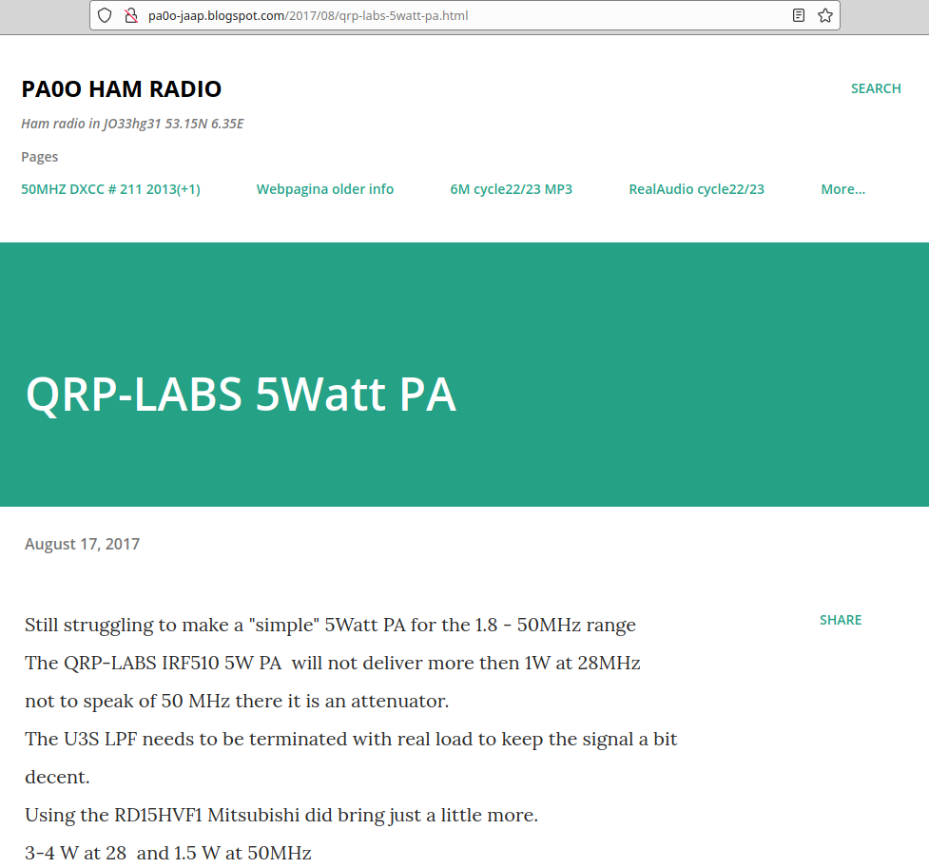
Info/Screenshot_2021-09-03_19-26-44.png
