kholia/HF-PA-v3/Info/TO-220 Heatsink + Insulator.jpg

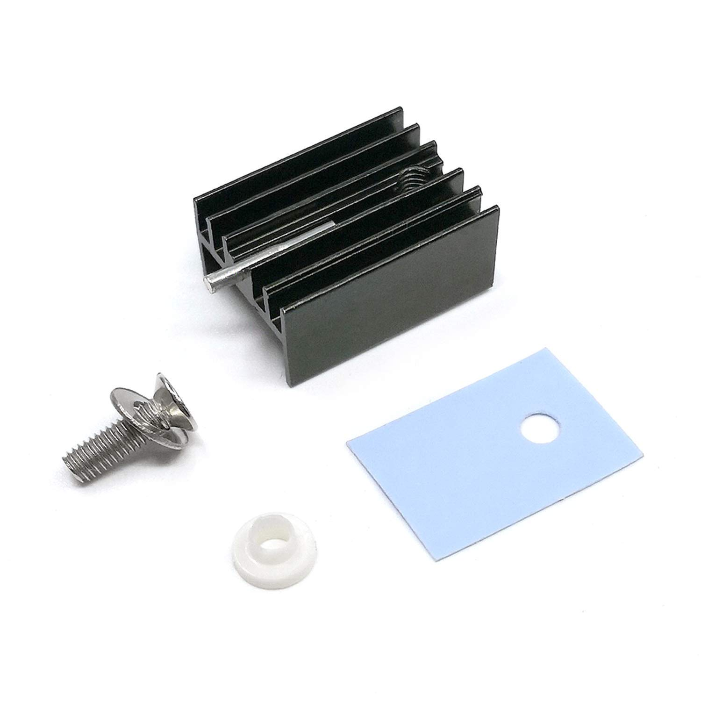
Info/TO-220 Heatsink + Insulator.jpg
