kholia/HF-PA-v3/Info/uSDXn_V1.9.1-20210905T234546Z-001.JPG

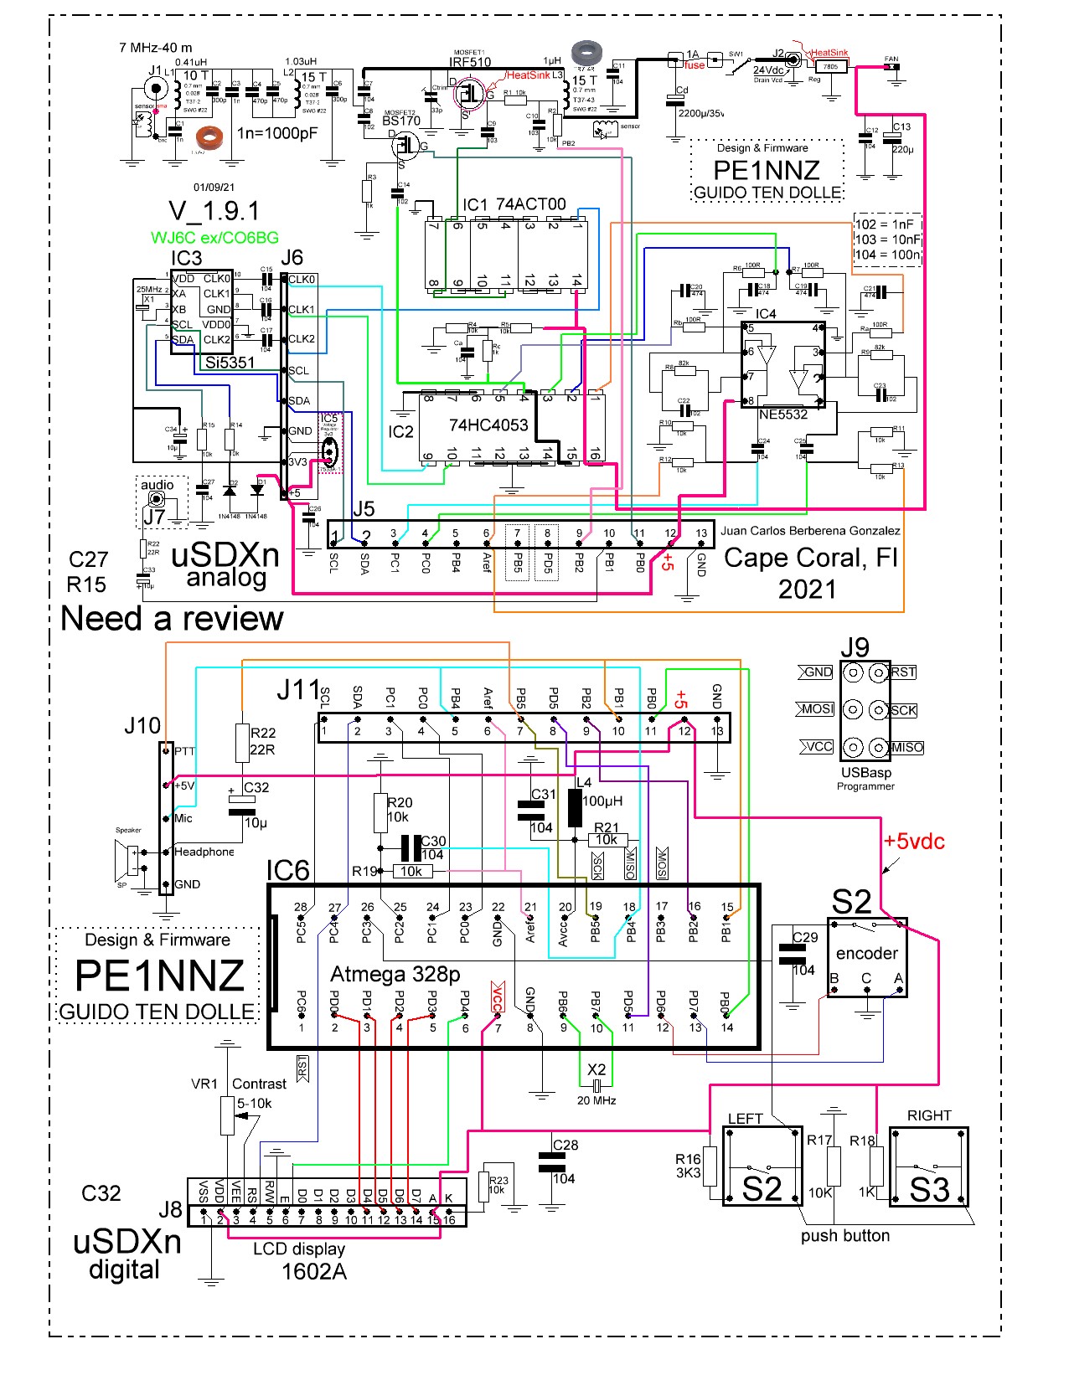
Info/uSDXn_V1.9.1-20210905T234546Z-001.JPG
