kholia/HF-PA-v3/RX-Reports/JP-Fest-Screenshot_2021-09-23_09-00-13.png

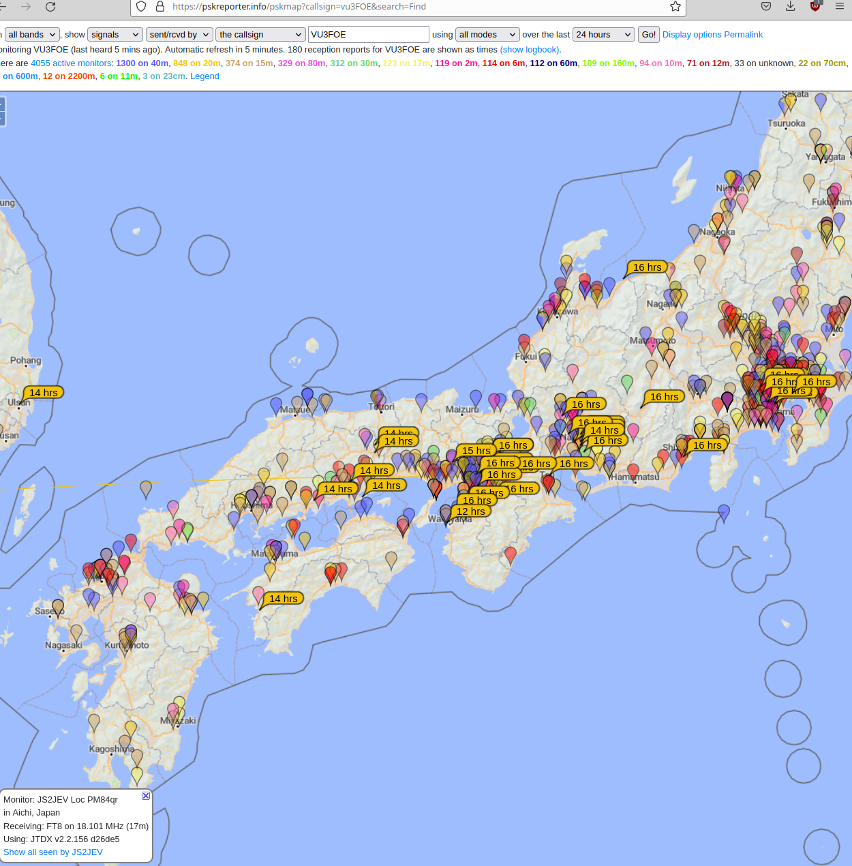
RX-Reports/JP-Fest-Screenshot_2021-09-23_09-00-13.png
