kholia/HF-PA-v3/RX-Reports/Screenshot_2021-09-21_21-24-22.png

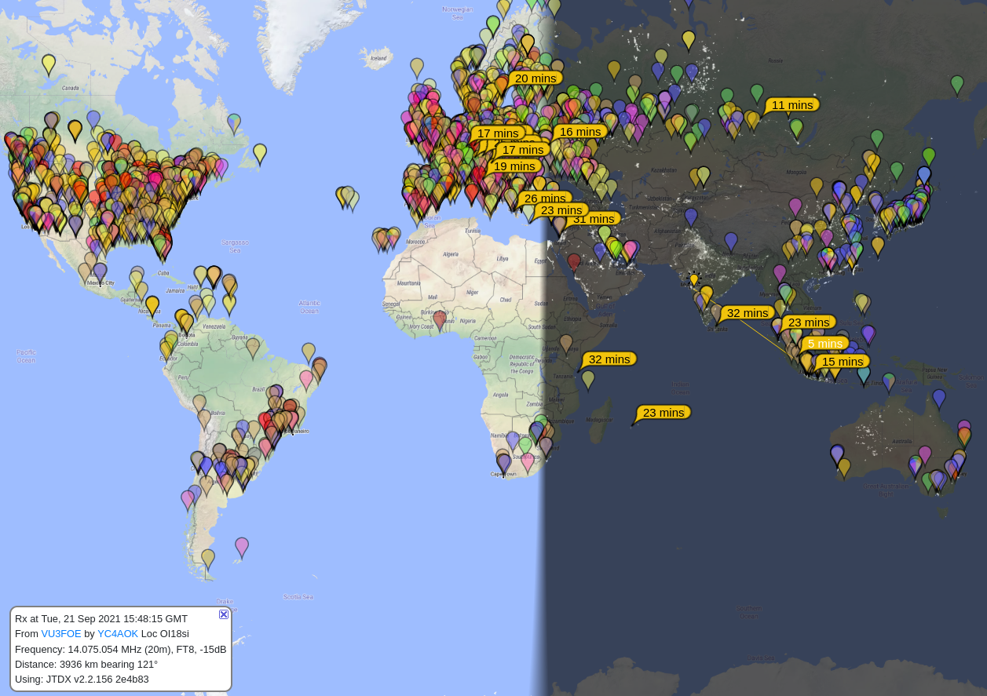
RX-Reports/Screenshot_2021-09-21_21-24-22.png
