kholia/HF-PA-v3/RX-Reports/Screenshot_2021-09-22_13-55-53.png

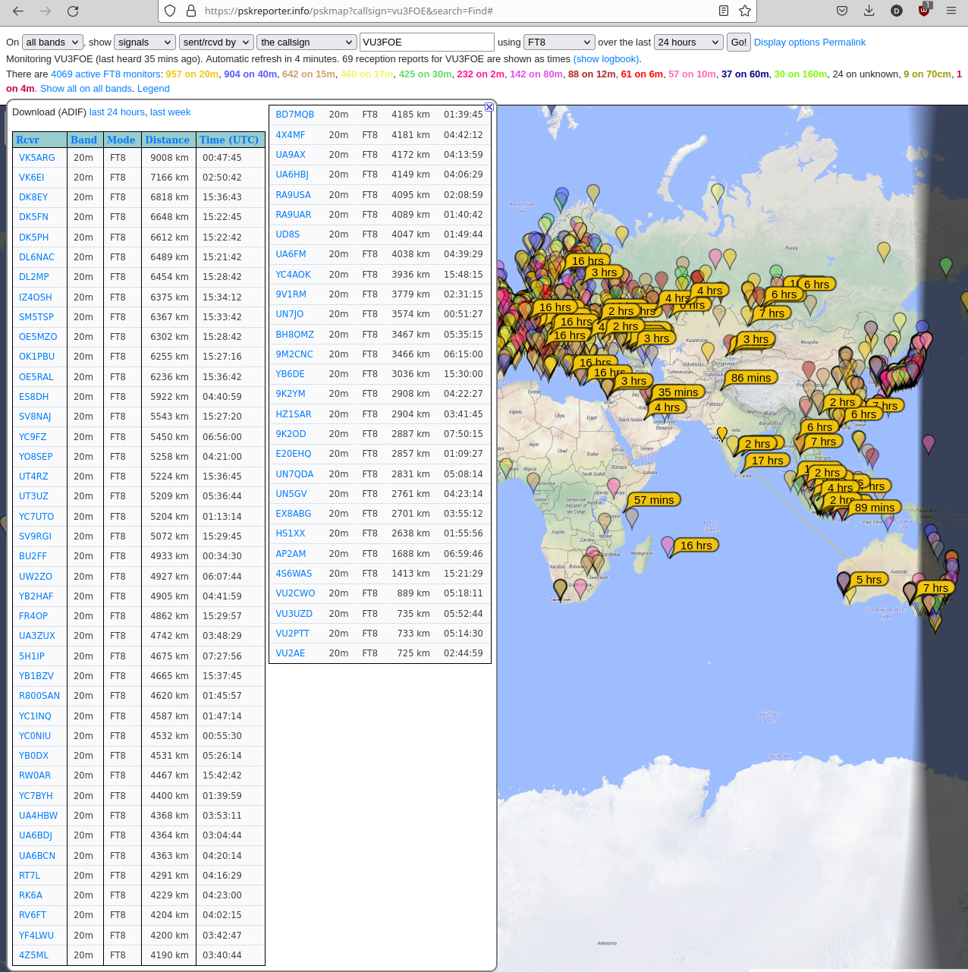
RX-Reports/Screenshot_2021-09-22_13-55-53.png
