kholia/HF-PA-v3/RX-Reports/Screenshot_2021-09-22_19-58-25.png

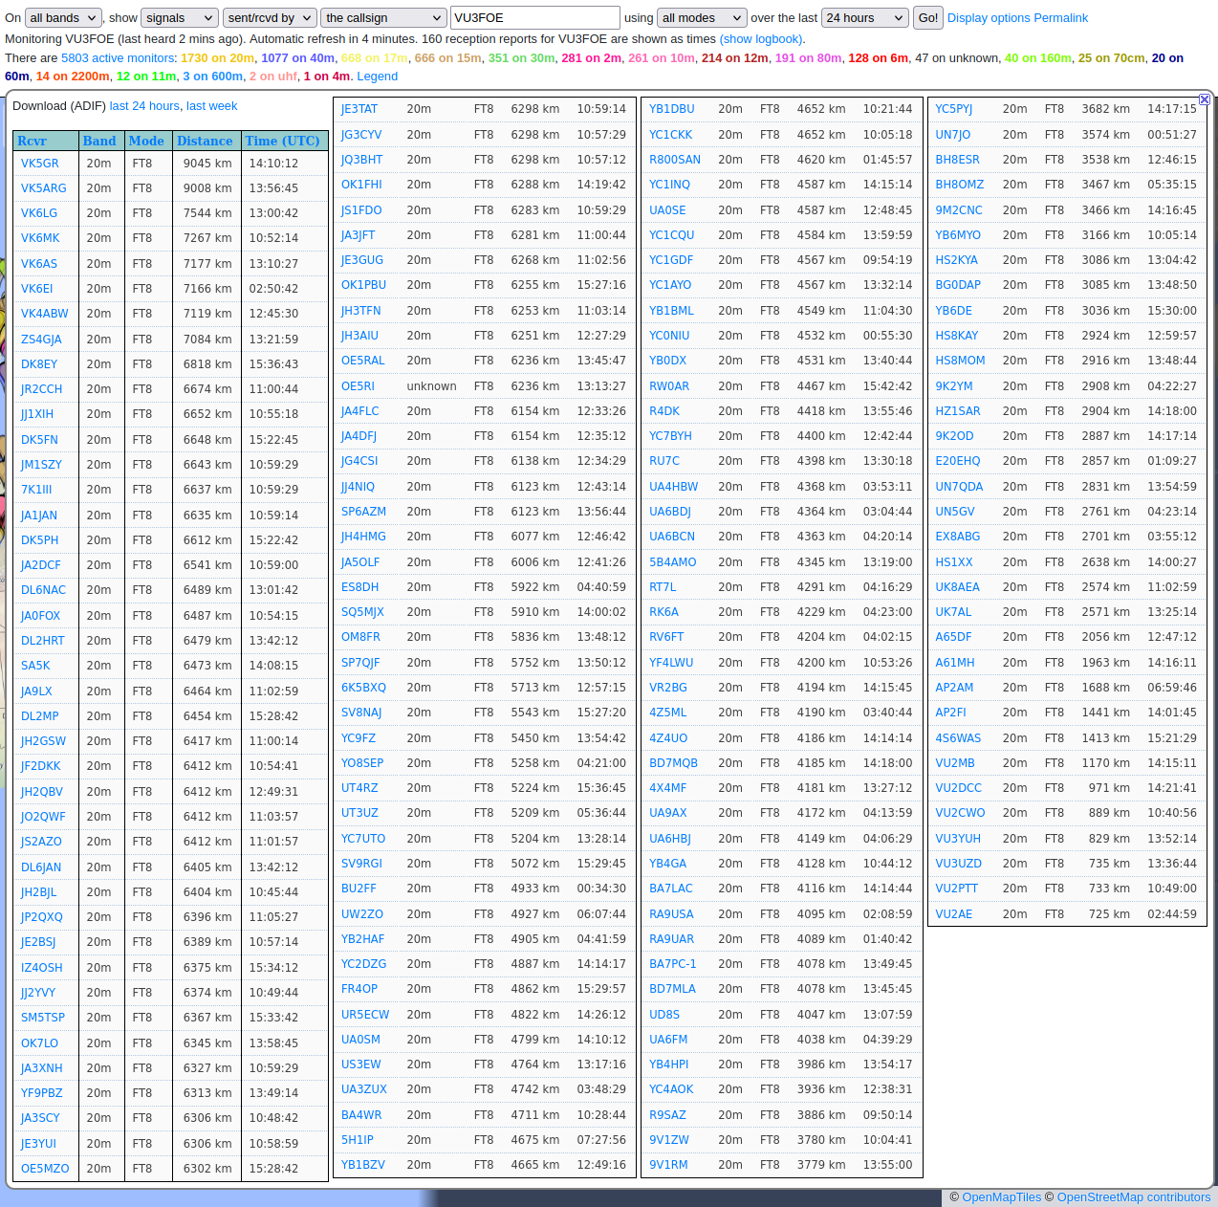
RX-Reports/Screenshot_2021-09-22_19-58-25.png
