kholia/HF-PA-v3/RX-Reports/Screenshot_2021-09-22_20-57-40.png

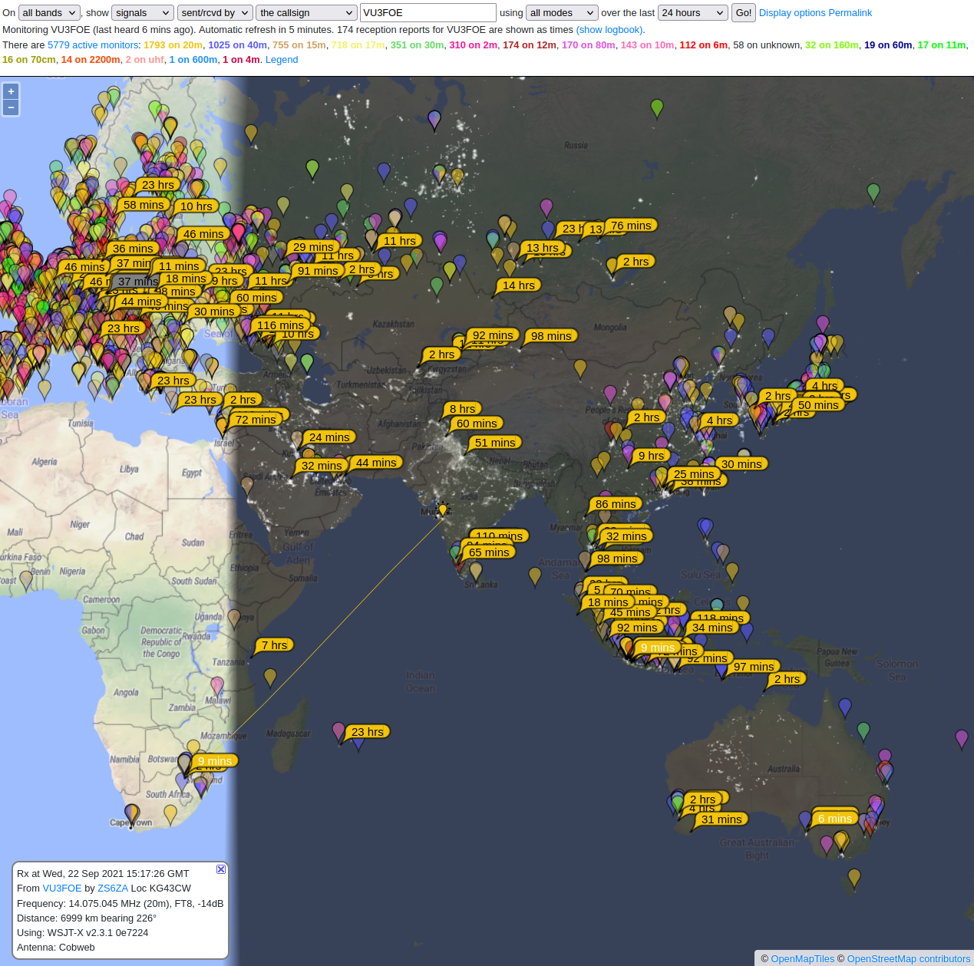
RX-Reports/Screenshot_2021-09-22_20-57-40.png
