kholia/HF-PA-v3/RX-Reports/Screenshot_2021-09-28_13-27-14.png

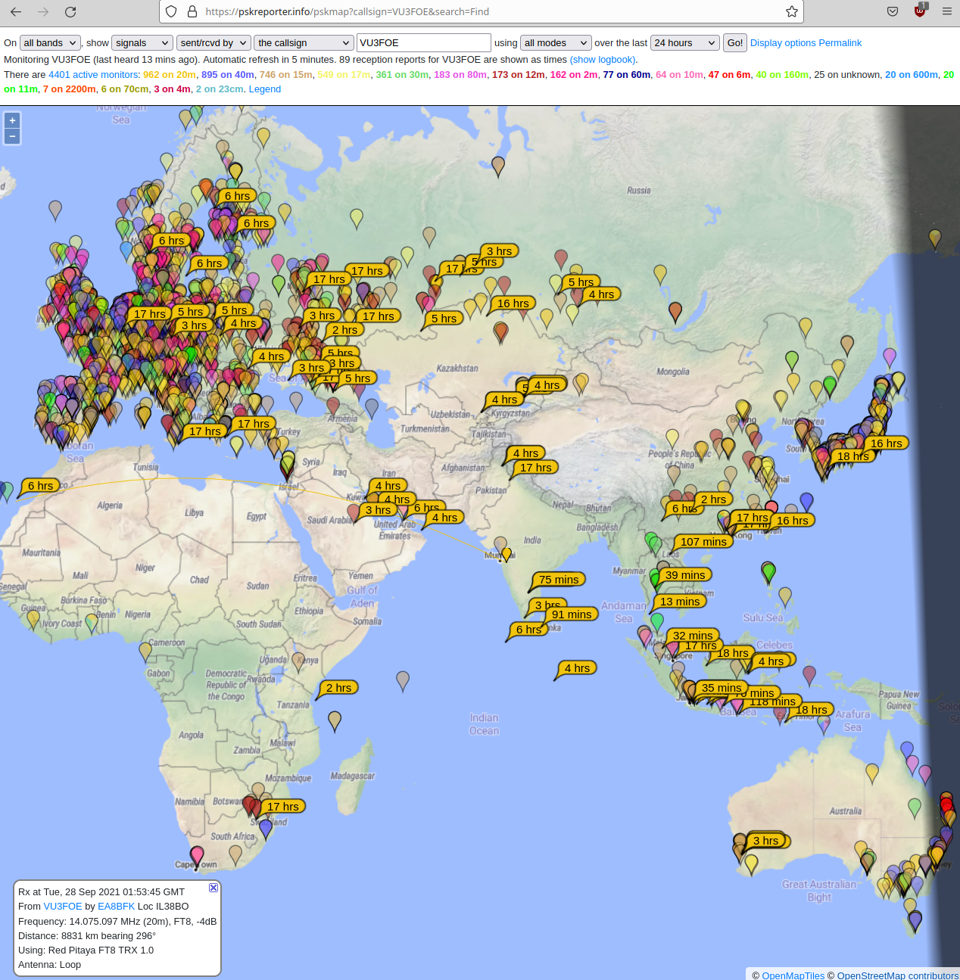
RX-Reports/Screenshot_2021-09-28_13-27-14.png
