kholia/HF-PA-v3/Socketable-Design/22-02-7033 Molex TO-220 Socket 4455 Series.jpg

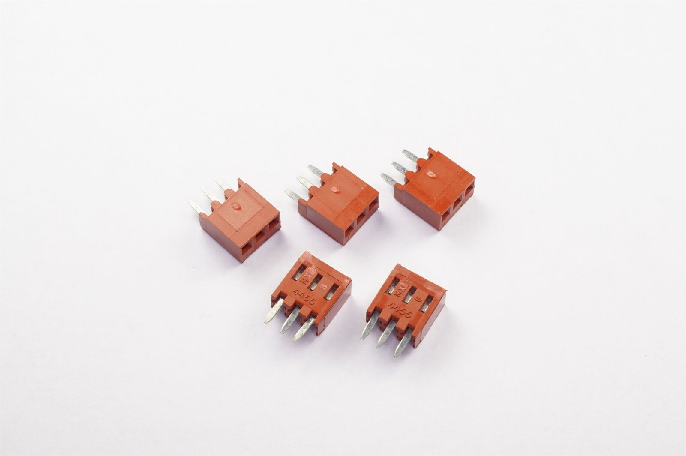
Socketable-Design/22-02-7033 Molex TO-220 Socket 4455 Series.jpg
