kholia/HF-PA-v3/Socketable-Design/900-0010182031-ND - 1.webp

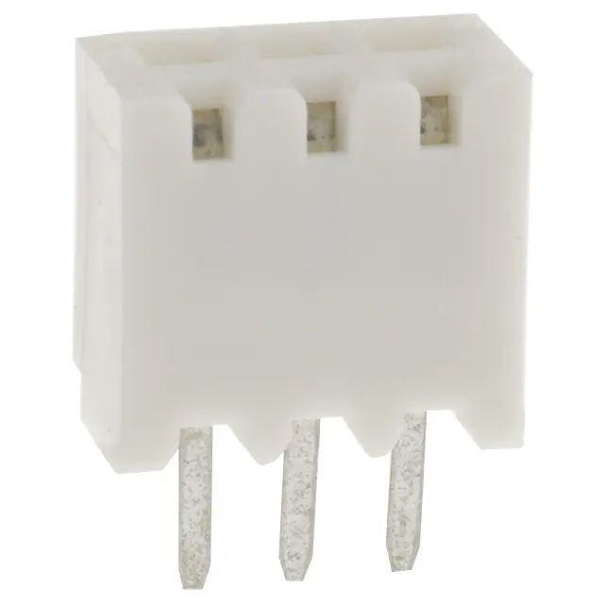
Socketable-Design/900-0010182031-ND - 1.webp
