kholia/HF-PA-v3/Socketable-Design/[Use this] SIP Socket.jpg

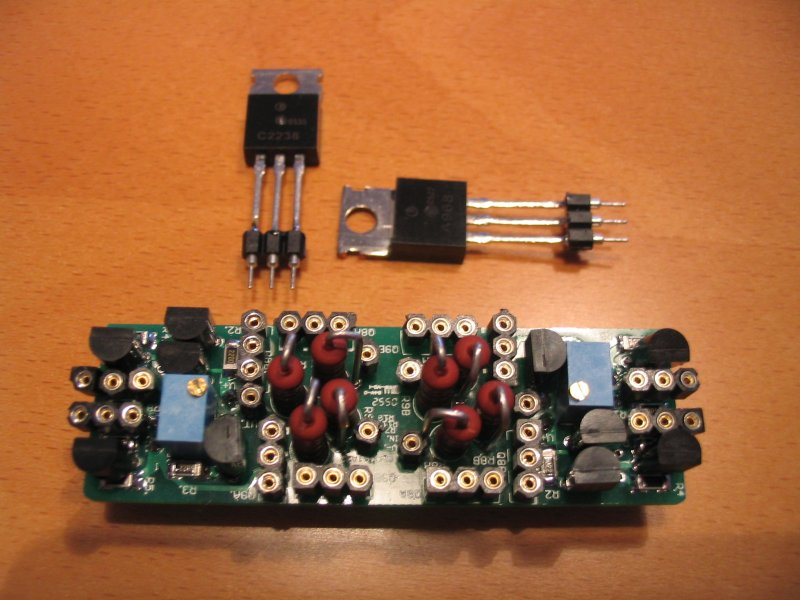
Socketable-Design/[Use this] SIP Socket.jpg
