kholia/HF-PA-v3/Socketable-Design/TTS4038series-dim.webp

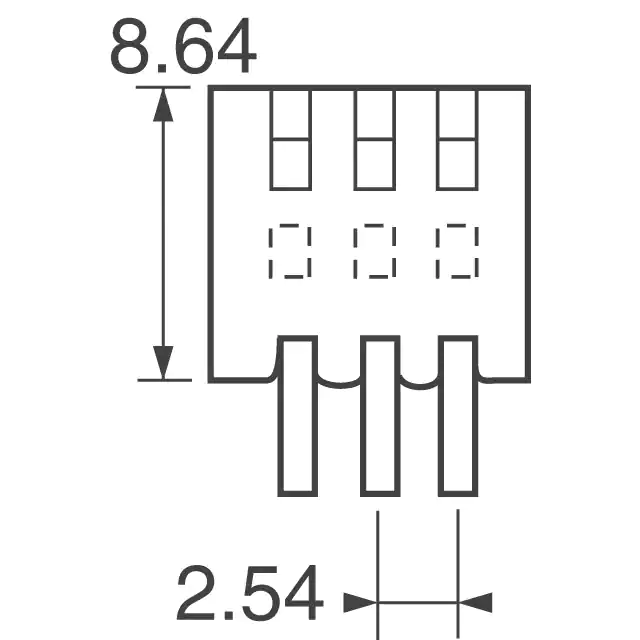
Socketable-Design/TTS4038series-dim.webp
