kholia/HF-PA-v3/Genuine-Vishay-IRF510/Vishay-IRF510PBF-RS-Components.jpg

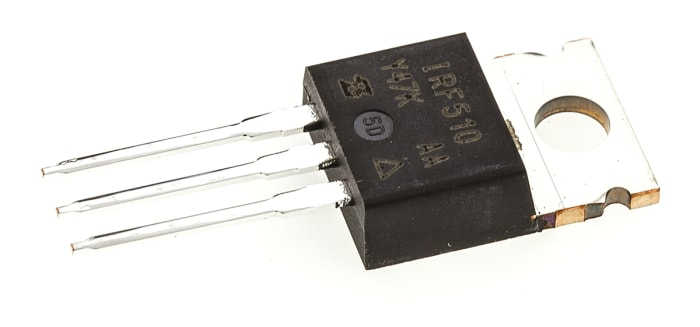
Genuine-Vishay-IRF510/Vishay-IRF510PBF-RS-Components.jpg
