kholia/HF-PA-v3/Info/150w-dc-dc-boost-converter-10-32v-to-12-35v-6a-step-up-adjustable-power-supply-module-800x800.jpg

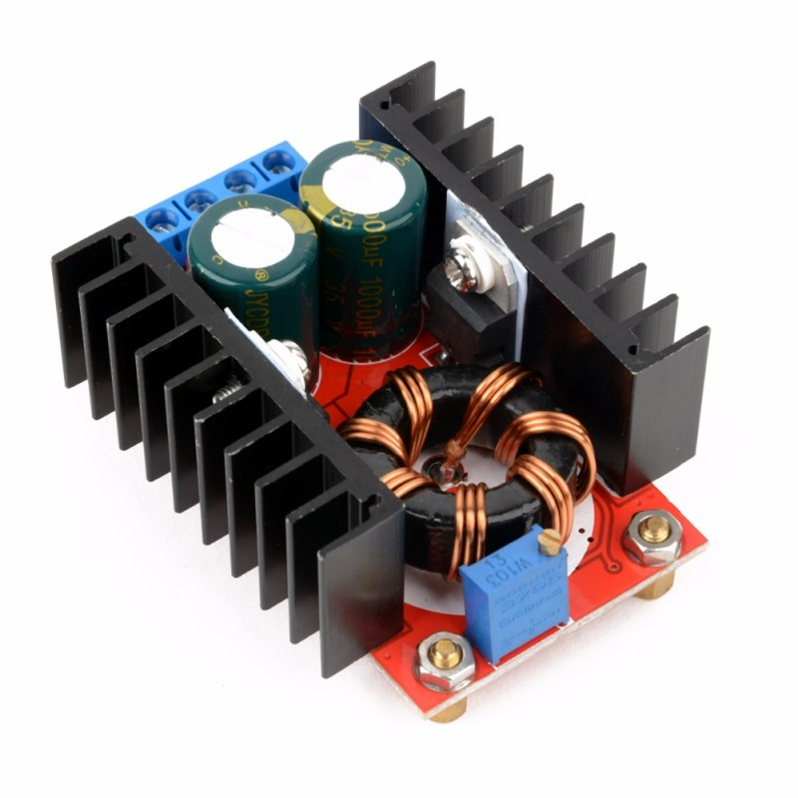
Info/150w-dc-dc-boost-converter-10-32v-to-12-35v-6a-step-up-adjustable-power-supply-module-800x800.jpg
