kholia/HF-PA-v3/HF-PA-Simulations/Matching N7VE's Results - Screenshot_2021-07-29_09-16-22.png

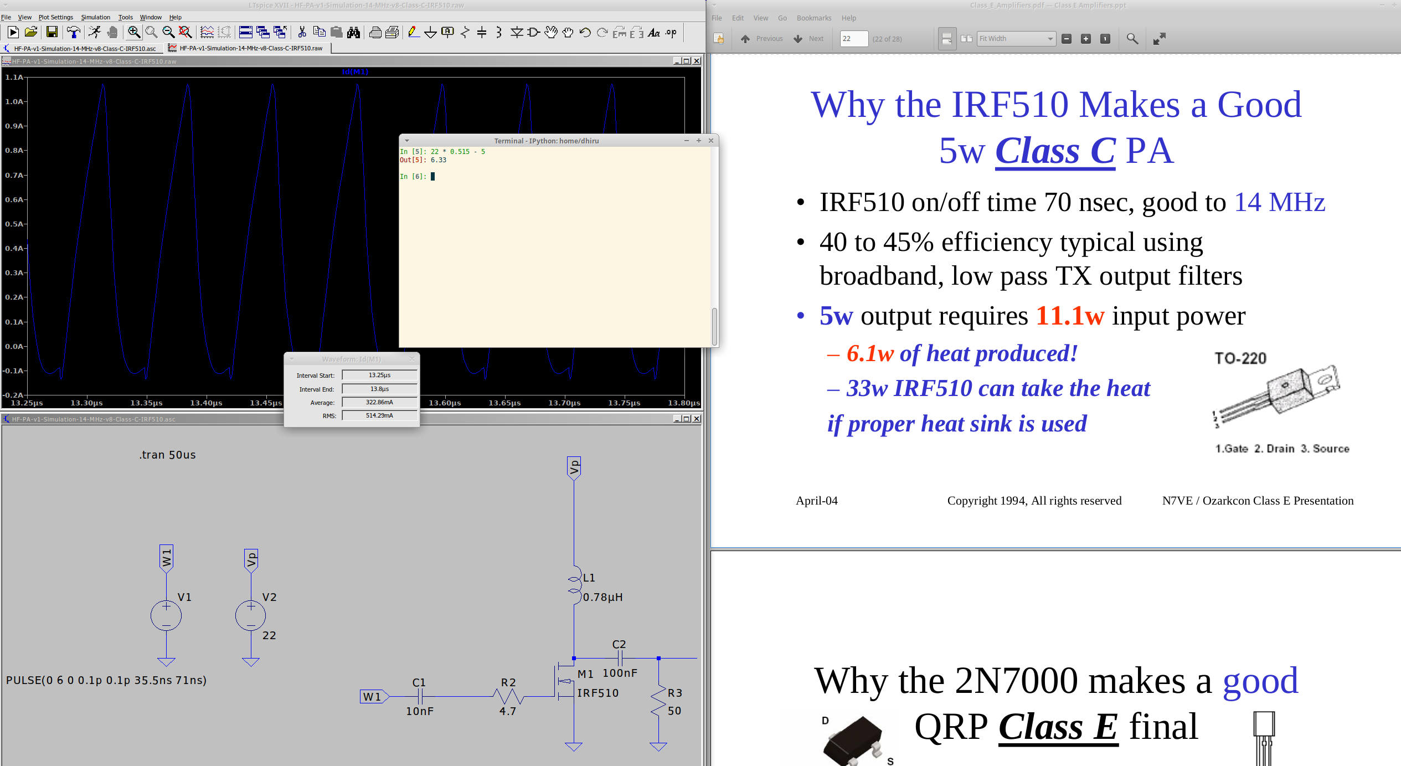
HF-PA-Simulations/Matching N7VE's Results - Screenshot_2021-07-29_09-16-22.png
