kholia/HF-PA-v3/HF-PA-Simulations/HF-PA-v1-Simulation-14-MHz-v8-Paul-RD16HHF1-Experiment.asc

C1: cap; 470nF
L1: ind; 0.8µH
M1: nmos; RD16HHF1
Q1: npn; 2N3904
R1: res; 1k
R2: res; 120
R3: res; 4.7
R4: res; 180
R5: res; 50
RV1: res; 2.81k
V1: voltage; PULSE(0 5 0 0.1p 0.1p 35ns 70ns)
V2: voltage; 12
V3: voltage; 6
V4: voltage; 0
Named nets: W1, Vp, 0, Vb, Vz
.tran 30us
Emitter Follower @ 14 MHz. Paul.
.include RD16HHF1.txt
