kholia/HF-PA-v3/HF-PA-Simulations/[Final] HF-PA-v1-Simulation-14-MHz-v8-Class-C-Biased-IRF510.asc

C1: cap; 10nF
C2: cap; 100nF
C3: cap; 100nF
L1: ind; 15µH
M1: nmos; IRF510
R1: res; 10k
R2: res; 4.7
R3: res; 50
U1: potentiometer; Rt=10K set=.14
V1: voltage; PULSE(0 6 0 0.1p 0.1p 35.5ns 71ns)
V2: voltage; 29
V4: voltage; 0
Named nets: W1, Vp, 0, Vz
.tran 1000us
