kholia/HF-PA-v3/HF-PA-Simulations/HF-PA-v1-Simulation-14-MHz-v8-Class-C-Bifilar-IRF510.asc

C1: cap; 10nF
C2: cap; 100nF
M1: nmos; IRF510
R2: res; 4.7
R3: res; 50
U1: bifilarCoil; L=0.39µH R=1 C=1nF K=0.9 Cp=10pF
V1: voltage; PULSE(0 6 0 0.1p 0.1p 35ns 70ns)
V2: voltage; 22
Named nets: W1, Vp, 0
.tran 50us
