kholia/HF-PA-v3/HF-PA-Simulations/HF-PA-v1-Simulation-14-MHz-v8-Class-D-IRF510.asc

C1: cap; 10nF
C2: cap; 100nF
L1: ind; 0.78µH
M1: nmos; IRF510
R1: res; 5.7k
R2: res; 4.7
R3: res; 50
RV1: res; 1k
V1: voltage; PULSE(0 5 0 0.1p 0.1p 35.5ns 71ns)
V2: voltage; 22
V4: voltage; 0
Named nets: W1, Vp, 0, Vz
.tran 100us
