kholia/HF-PA-v3/HF-PA-Simulations/HF-PA-v1-Simulation-7-MHz-v8-Class-C-IRF510.asc

C1: cap; 10nF
C2: cap; 100nF
L1: ind; 10µH
M1: nmos; IRF510
R2: res; 4.7
R3: res; 50
V1: voltage; PULSE(0 6 0 0.1p 0.1p 71ns 142ns)
V2: voltage; 13.8
Named nets: W1, Vp, 0
.tran 50us
