kholia/HF-PA-v3/HF-PA-Simulations/HF-PA-v1-Simulation-7-MHz-v8-Direct-RD16HHF1-Easy-5W.asc

C1: cap; 10nF
L1: ind; 0.8µH
M1: nmos; RD16HHF1
R1: res; 50
V1: voltage; PULSE(0 6 0 0.1p 0.1p 71ns 142ns)
V2: voltage; 12
V3: voltage; 5
V4: voltage; 0
Named nets: W1, Vp, 0, Vb, Vz
.tran 10us
.include RD16HHF1.txt
Direct Drive @ 14 MHz.
