kholia/HF-PA-v3/HF-PA-Simulations/Miro-Circuit.asc

C1: cap; 10nF
C2: cap; 100nF
L1: ind; 50.40µH
M1: nmos; IRF510
R2: res; 4.7
R3: res; 50
V1: voltage; PULSE(0 5 0 0.1p 0.1p 35ns 70ns)
V2: voltage; 13.8
Named nets: W1, Vp, 0
.tran 50us
.include RD16HHF1.txt
